djspawnbrest/ESP32AY/PCB/revD2/KiCad/3d/ZX62D-B-5P8.step

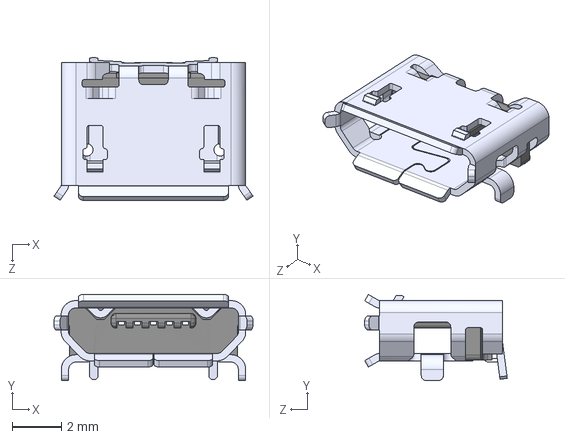
[picture p22: CAD file, 2024-06-26]
PCB/revD2/KiCad/3d/ZX62D-B-5P8.step
8.09 x 3.50 x 5.80 mm
