djspawnbrest/ESP32AY/PCB/revD2/KiCad/3d/35RAPC2BHN2.step

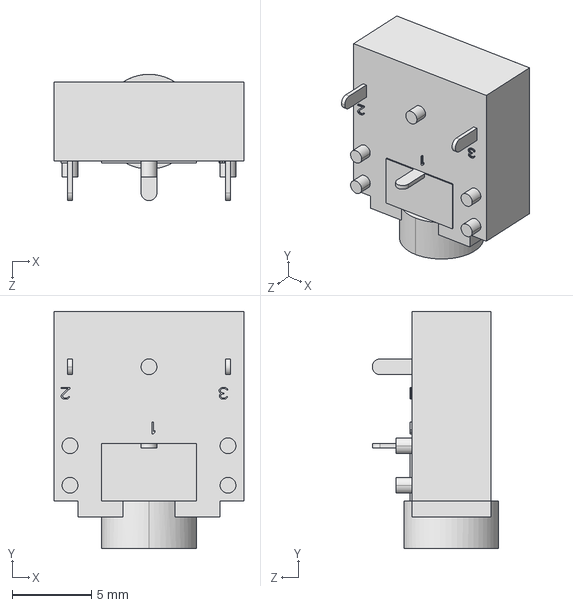
[picture p24: CAD file, 2024-06-26]
PCB/revD2/KiCad/3d/35RAPC2BHN2.step
12.0 x 15.0 x 8.00 mm
