djspawnbrest/ESP32AY/PCB/revD2/KiCad/3d/TPA6130A2RTJTG4.step

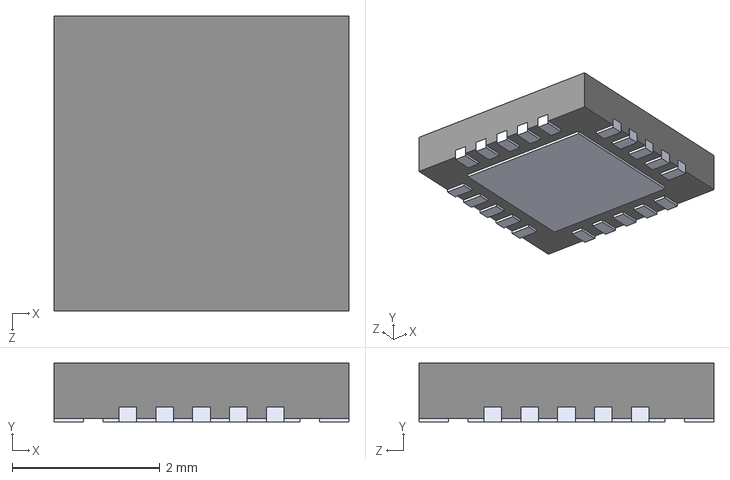
[picture p25: CAD file, 2024-06-26]
PCB/revD2/KiCad/3d/TPA6130A2RTJTG4.step
4.00 x 0.8 x 4.00 mm
