djspawnbrest/ESP32AY/PCB/revD2/KiCad/3d/FSM8J.STEP

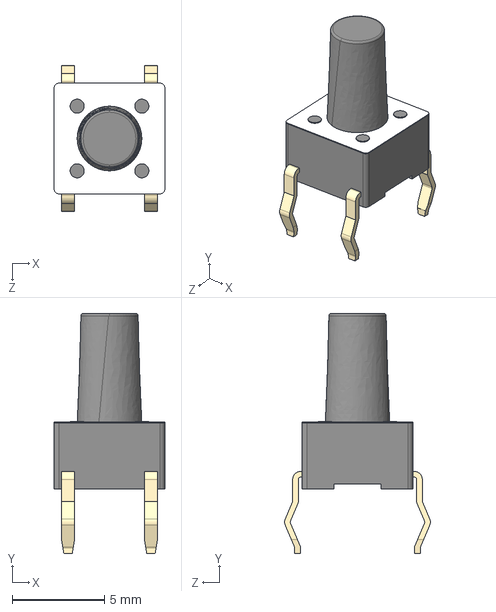
[picture p26: CAD file, 2024-06-26]
PCB/revD2/KiCad/3d/FSM8J.STEP
5.99 x 13.0 x 7.90 mm
