djspawnbrest/ESP32AY/PCB/revD2/KiCad/3d/Tactal Switch -Thru (6mmx 6mmx9.0mm).stp

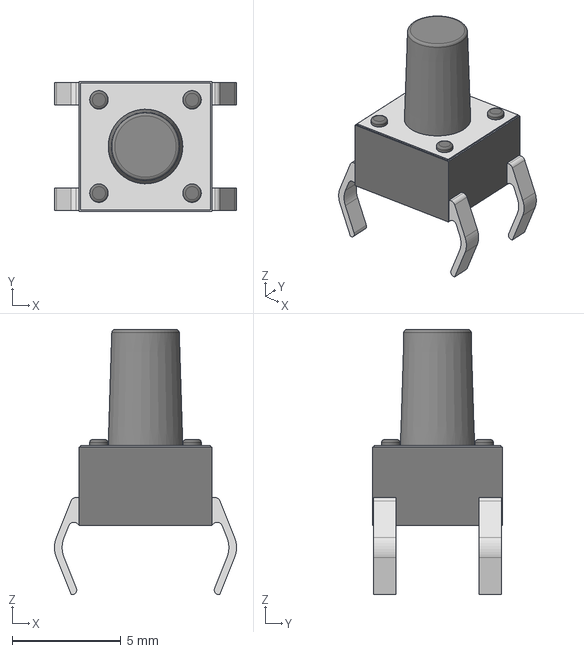
[picture p27: CAD file, 2024-06-26]
PCB/revD2/KiCad/3d/Tactal Switch -Thru (6mmx 6mmx9.0mm).stp
8.37 x 5.99 x 12.2 mm
