djspawnbrest/ESP32AY/PCB/revD2/KiCad/3d/SS14.step

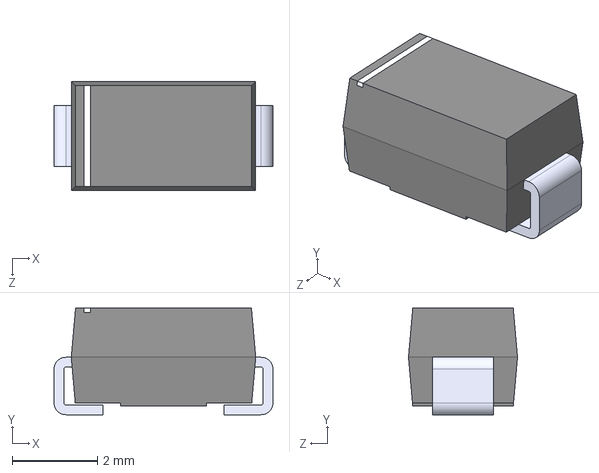
[picture p28: CAD file, 2024-06-26]
PCB/revD2/KiCad/3d/SS14.step
5.14 x 2.50 x 2.56 mm
