djspawnbrest/ESP32AY/PCB/revD2/KiCad/3d/tft1.8.step

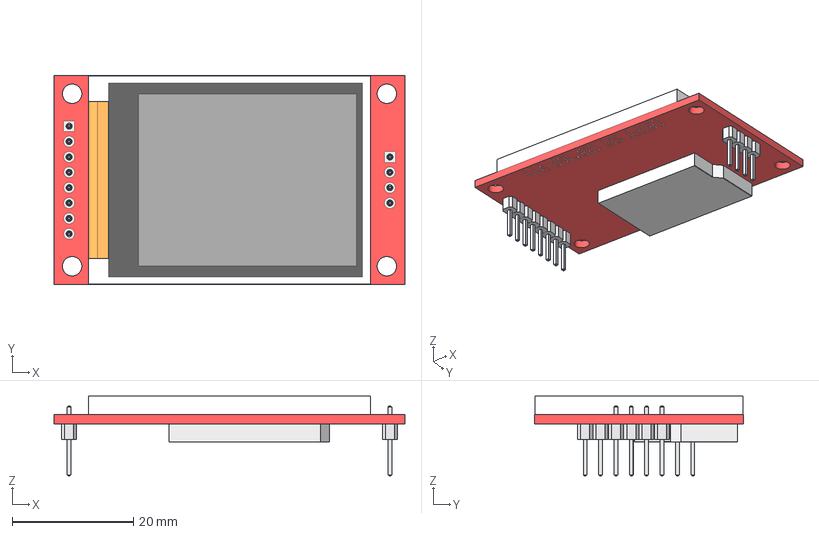
[picture p29: CAD file, 2024-06-26]
PCB/revD2/KiCad/3d/tft1.8.step
58.0 x 34.5 x 13.1 mm
1.8 TFT 128x160 SPI1_001
8pins1_001
4pins1_001
