djspawnbrest/ESP32AY/PCB/revD2/KiCad/3d/EG1213.step

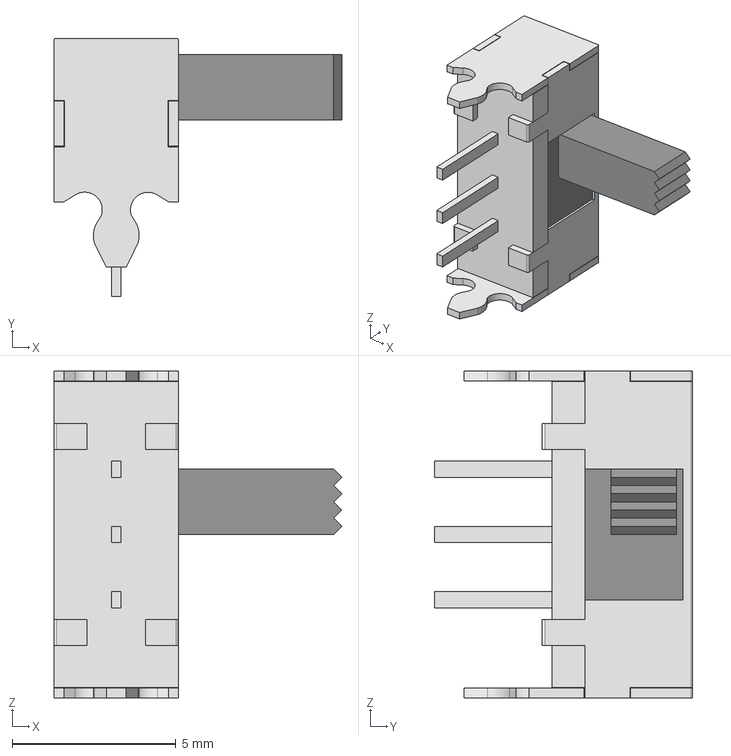
[picture p30: CAD file, 2024-06-26]
PCB/revD2/KiCad/3d/EG1213.step
8.80 x 7.90 x 10.00 mm
