djspawnbrest/ESP32AY/PCB/revD2/KiCad/3d/ME2108A33P.step

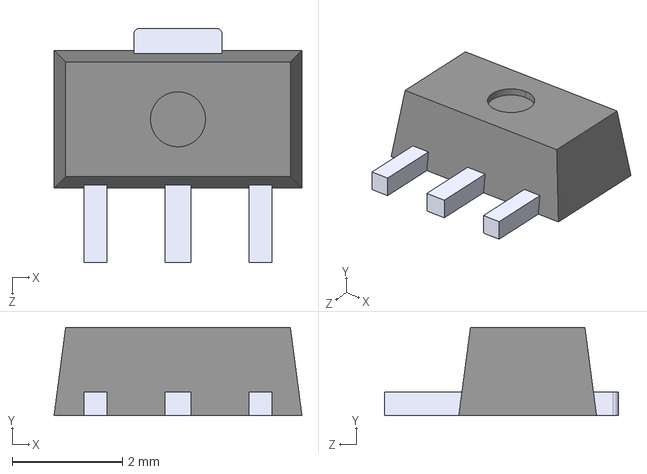
[picture p31: CAD file, 2024-06-26]
PCB/revD2/KiCad/3d/ME2108A33P.step
4.50 x 1.60 x 4.25 mm
