djspawnbrest/ESP32AY/PCB/revD2/KiCad/3d/GMT177-01.iges

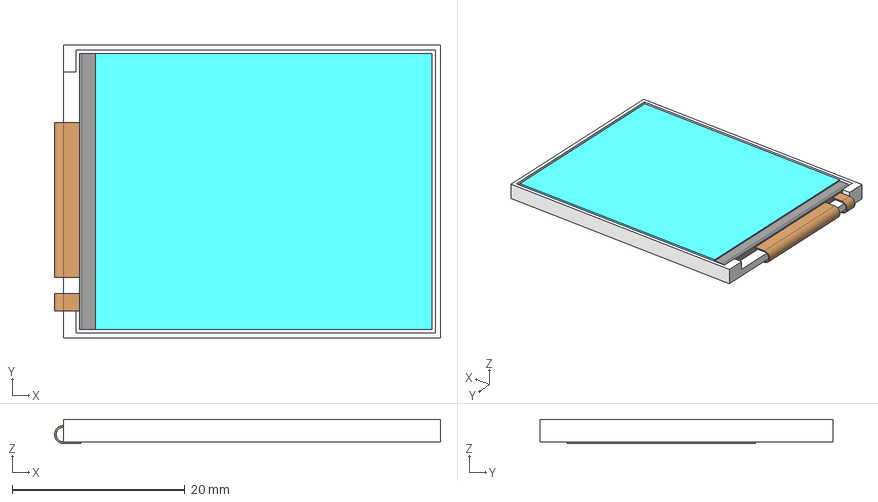
[picture p32: CAD file, 2024-06-26]
PCB/revD2/KiCad/3d/GMT177-01.iges
44.7 x 34.0 x 2.80 mm
