djspawnbrest/ESP32AY/PCB/revD2/KiCad/3d/audio_3.5mm_trrs.STEP

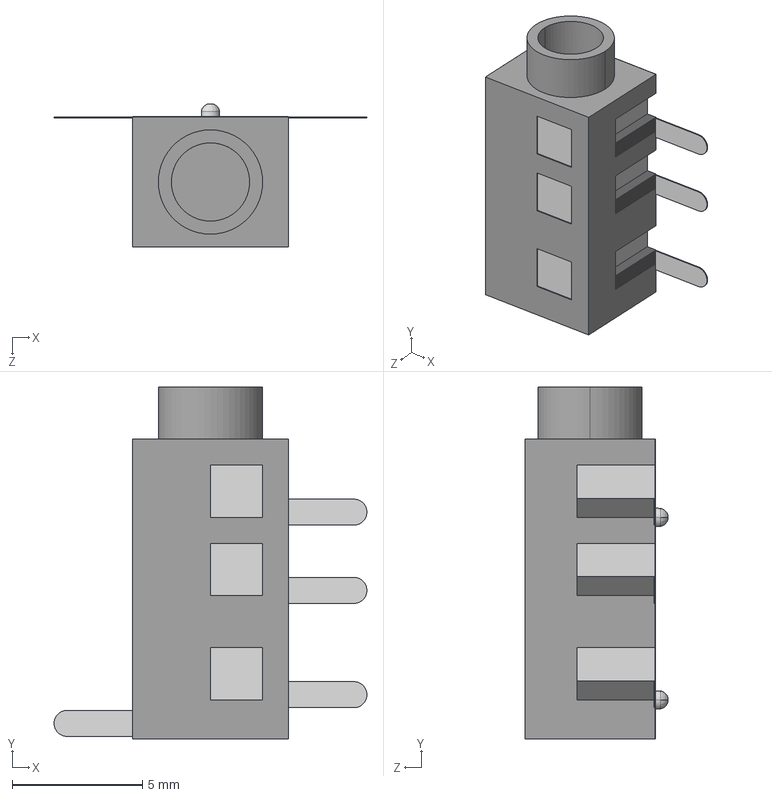
[picture p33: CAD file, 2024-06-26]
PCB/revD2/KiCad/3d/audio_3.5mm_trrs.STEP
12.0 x 13.5 x 5.50 mm
Composant1.step
audio_3.5mm_trrs.step
audio_3.5mm_trrs-0.step
audio_3.5mm_trrs-1.step
audio_3.5mm_trrs-2.step
audio_3.5mm_trrs-3.step
audio_3.5mm_trrs-4.step
audio_3.5mm_trrs-5.step
audio_3.5mm_trrs-6.step
audio_3.5mm_trrs-7.step
audio_3.5mm_trrs-8.step
audio_3.5mm_trrs-9.step
audio_3.5mm_trrs-10.step
audio_3.5mm_trrs-11.step
audio_3.5mm_trrs-12.step
audio_3.5mm_trrs-13.step
