djspawnbrest/ESP32AY/PCB/revD2/KiCad/3d/ArduinoMega_STEP_AP203.STEP

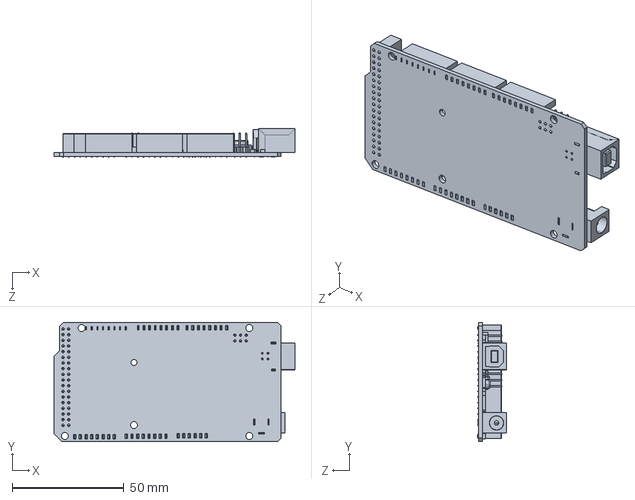
[picture p34: CAD file, 2024-06-26]
PCB/revD2/KiCad/3d/ArduinoMega_STEP_AP203.STEP
107.9 x 53.4 x 13.0 mm
