djspawnbrest/ESP32AY/PCB/revD2/KiCad/3d/EC11-THT-15_rotated.step

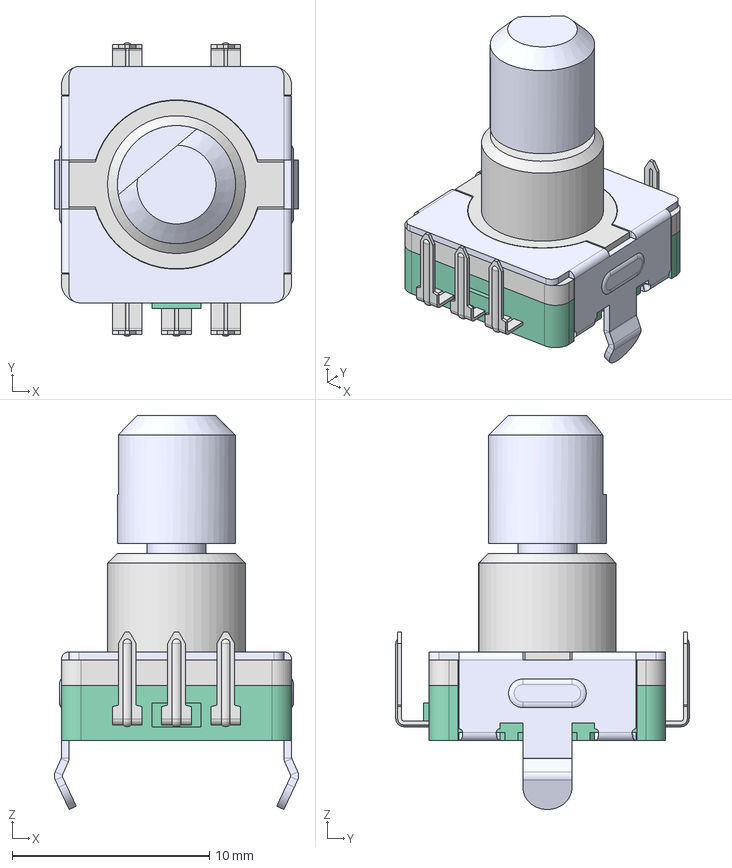
[picture p35: CAD file, 2024-06-26]
PCB/revD2/KiCad/3d/EC11-THT-15_rotated.step
12.4 x 14.9 x 20.0 mm
EC11-Base
EC11-Shaft-F
EC11-Housing-THT
