djspawnbrest/ESP32AY/PCB/revD2/KiCad/3d/TP4056.step

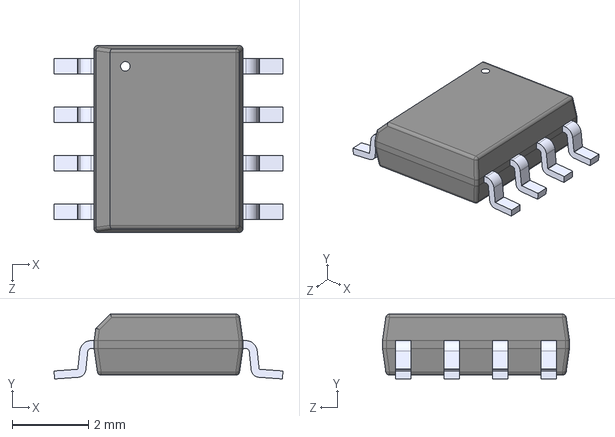
[picture p36: CAD file, 2024-06-26]
PCB/revD2/KiCad/3d/TP4056.step
6.00 x 1.70 x 4.90 mm
