djspawnbrest/ESP32AY/src/players/PT3Play.h

//Pro tracker 3.x player was written by S.V. Bulba.

//Table #0 of Pro Tracker 3.3x - 3.4r
const unsigned short PT3NoteTable_PT_33_34r[] =
{ 0x0C21, 0x0B73, 0x0ACE, 0x0A33, 0x09A0, 0x0916, 0x0893, 0x0818, 0x07A4, 0x0736, 0x06CE, 0x066D, 0x0610, 0x05B9, 0x0567, 0x0519, 0x04D0, 0x048B, 0x0449, 0x040C, 0x03D2, 0x039B, 0x0367, 0x0336, 0x0308, 0x02DC, 0x02B3, 0x028C, 0x0268, 0x0245, 0x0224, 0x0206, 0x01E9, 0x01CD, 0x01B3, 0x019B, 0x0184, 0x016E, 0x0159, 0x0146, 0x0134, 0x0122, 0x0112, 0x0103, 0x00F4, 0x00E6, 0x00D9, 0x00CD, 0x00C2, 0x00B7, 0x00AC, 0x00A3, 0x009A, 0x0091, 0x0089, 0x0081, 0x007A, 0x0073, 0x006C, 0x0066, 0x0061, 0x005B, 0x0056, 0x0051, 0x004D, 0x0048, 0x0044, 0x0040, 0x003D, 0x0039, 0x0036, 0x0033, 0x0030, 0x002D, 0x002B, 0x0028, 0x0026, 0x0024, 0x0022, 0x0020, 0x001E, 0x001C, 0x001B, 0x0019, 0x0018, 0x0016, 0x0015, 0x0014, 0x0013, 0x0012, 0x0011, 0x0010, 0x000F, 0x000E, 0x000D, 0x000C };

//{Table #0 of Pro Tracker 3.4x - 3.5x}
const unsigned short PT3NoteTable_PT_34_35[] =
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
#define PT3_SamplesPointers(x) (header->PT3_SamplesPointers0 [(x) * 2] | (header->PT3_SamplesPointers0 [(x) * 2 + 1] << 8))
#define PT3_OrnamentsPointers(x) (header->PT3_OrnamentsPointers0 [(x) * 2] | (header->PT3_OrnamentsPointers0 [(x) * 2 + 1] << 8))

struct PT3_Channel_Parameters
{
    unsigned short Address_In_Pattern, OrnamentPointer, SamplePointer, Ton;
    unsigned char Loop_Ornament_Position, Ornament_Length, Position_In_Ornament, Loop_Sample_Position, Sample_Length, Position_In_Sample, Volume, Number_Of_Notes_To_Skip, Note, Slide_To_Note, Amplitude;
    bool Envelope_Enabled, Enabled, SimpleGliss;
    short Current_Amplitude_Sliding, Current_Noise_Sliding, Current_Envelope_Sliding, Ton_Slide_Count, Current_OnOff, OnOff_Delay, OffOn_Delay, Ton_Slide_Delay, Current_Ton_Sliding, Ton_Accumulator, Ton_Slide_Step, Ton_Delta;
    signed char Note_Skip_Counter;
};

struct PT3_Parameters
{
    unsigned char Env_Base_lo;
    unsigned char Env_Base_hi;
    short Cur_Env_Slide, Env_Slide_Add;
    signed char Cur_Env_Delay, Env_Delay;
    unsigned char Noise_Base, Delay, AddToNoise, DelayCounter, CurrentPosition;
    int Version;
};

struct PT3_SongInfo
{
    PT3_Parameters PT3;
    PT3_Channel_Parameters PT3_A, PT3_B, PT3_C;
};

#define PT3_A ((PT3_SongInfo *)data)->PT3_A
#define PT3_B ((PT3_SongInfo *)data)->PT3_B
#define PT3_C ((PT3_SongInfo *)data)->PT3_C
#define PT3 ((PT3_SongInfo *)data)->PT3

#define GET_COMMON_VARS(x) \
    unsigned char *module;\
    PT3_File *header;\
    void *data;\
    if(!info.is_ts || x == 0)\
    {\
        module = info.module;\
        header = (PT3_File *)info.module;\
        data = info.data;\
    }\
    else\
    {\
        module = info.module1;\
        header = (PT3_File *)info.module1;\
        data = info.data1;\
    }

bool PT3_Detect(unsigned char *module, unsigned long length);

unsigned char *PT3_FindSig(unsigned char *buffer, long length)
{
    char sig[] =
    { 0x50, 0x72, 0x6f, 0x54, 0x72, 0x61, 0x63, 0x6b, 0x65, 0x72, 0x20, 0x33, 0x2e };
    char sig1[] =
    { 0x56, 0x6f, 0x72, 0x74, 0x65, 0x78, 0x20, 0x54, 0x72, 0x61, 0x63, 0x6b, 0x65, 0x72, 0x20, 0x49, 0x49 };
    if(length < sizeof(sig) || length < sizeof(sig1))
        return 0;
    unsigned char *ptr = buffer;
    unsigned long remaining = length - sizeof(sig);
    while(remaining > sizeof(sig))
    {
        if(!memcmp(ptr, sig, sizeof(sig)) || !memcmp(ptr, sig1, sizeof(sig1))) //found
        {
            return ptr;
        }
        ptr++;
        remaining--;
    }
    return 0;
}

void PT3_Init(AYSongInfo &info)
{
    int i;
    unsigned char b;
    unsigned char *module = info.module;
    PT3_File *header = (PT3_File *)module;
    if(info.data)
    {
        delete (PT3_SongInfo *)info.data;
        info.data = 0;
    }
    if(info.data1)
    {
        delete (PT3_SongInfo *)info.data1;
        info.data1 = 0;
    }
    info.data = (void *)new PT3_SongInfo;
    if(!info.data)
        return;
    memset(info.data, 0, sizeof(PT3_SongInfo));

    int version = 6;

    if((header->PT3_MusicName[13] >= '0') && (header->PT3_MusicName[13] <= '9'))
    {
        version = header->PT3_MusicName[13] - 0x30;
    }
    
    bool is_ts_37 = false;
    if(version >= 7)
    {
        for(int pos = 0; pos < header->PT3_NumberOfPositions && pos < 256; pos++)
        {
            int pat_idx = header->PT3_PositionList[pos] / 3;
            if(pat_idx >= 24 && pat_idx < 48)
            {
                is_ts_37 = true;
                break;
            }
        }
    }
    
    unsigned char *ptr = PT3_FindSig(module + 0x63, info.module_len - 0x63);
    if((unsigned long)ptr > 0 || is_ts_37)
    {
        info.is_ts = true;
        if(is_ts_37 && (unsigned long)ptr == 0)
        {
            info.module1 = module;
        }
        else
        {
            info.module1 = ptr;
            is_ts_37 = false;
        }
        info.data1 = (void *)new PT3_SongInfo;
        if(!info.data1)
        {
            delete (PT3_SongInfo *)info.data;
            info.data = 0;
            return;
        }
        memset(info.data1, 0, sizeof(PT3_SongInfo));
    }

    void *data = info.data;
    module = info.module;

    for(unsigned long y = 0; y < 2; y++)
    {
        PT3.CurrentPosition = 0;
        i = header->PT3_PositionList[0];
        b = header->PT3_MusicName[0x62];
        if(b != 0x20)
        {
            int max_pos = b * 3 - 3;
            i = max_pos - i;
        }
        if(is_ts_37 && y == 1)
        {
            int pat_idx = i / 3;
            pat_idx = 47 - pat_idx;
            i = pat_idx * 3;
        }
        PT3.Version = version;
        PT3.DelayCounter = 1;
        PT3.Delay = header->PT3_Delay;
        PT3_A.Address_In_Pattern = ay_sys_getword(&module[PT3_PatternsPointer + i * 2]);
        PT3_B.Address_In_Pattern = ay_sys_getword(&module[PT3_PatternsPointer + i * 2 + 2]);
        PT3_C.Address_In_Pattern = ay_sys_getword(&module[PT3_PatternsPointer + i * 2 + 4]);

        PT3_A.OrnamentPointer = PT3_OrnamentsPointers(0);
        PT3_A.Loop_Ornament_Position = module[PT3_A.OrnamentPointer];
        PT3_A.OrnamentPointer++;
        PT3_A.Ornament_Length = module[PT3_A.OrnamentPointer];
        PT3_A.OrnamentPointer++;
        PT3_A.SamplePointer = PT3_SamplesPointers(1);
        PT3_A.Loop_Sample_Position = module[PT3_A.SamplePointer];
        PT3_A.SamplePointer++;
        PT3_A.Sample_Length = module[PT3_A.SamplePointer];
        PT3_A.SamplePointer++;
        PT3_A.Volume = 15;
        PT3_A.Note_Skip_Counter = 1;

        PT3_B.OrnamentPointer = PT3_A.OrnamentPointer;
        PT3_B.Loop_Ornament_Position = PT3_A.Loop_Ornament_Position;
        PT3_B.Ornament_Length = PT3_A.Ornament_Length;
        PT3_B.SamplePointer = PT3_A.SamplePointer;
        PT3_B.Loop_Sample_Position = PT3_A.Loop_Sample_Position;
        PT3_B.Sample_Length = PT3_A.Sample_Length;
        PT3_B.Volume = 15;
        PT3_B.Note_Skip_Counter = 1;

        PT3_C.OrnamentPointer = PT3_A.OrnamentPointer;
        PT3_C.Loop_Ornament_Position = PT3_A.Loop_Ornament_Position;
        PT3_C.Ornament_Length = PT3_A.Ornament_Length;
        PT3_C.SamplePointer = PT3_A.SamplePointer;
        PT3_C.Loop_Sample_Position = PT3_A.Loop_Sample_Position;
        PT3_C.Sample_Length = PT3_A.Sample_Length;
        PT3_C.Volume = 15;
        PT3_C.Note_Skip_Counter = 1;
        if(!info.is_ts)
            break;
        data = info.data1;
        if(!is_ts_37)
        {
            module = info.module1;
            header = (PT3_File *)module;
        }
    }

    ay_resetay(&info, 0);
    ay_resetay(&info, 1);
}

int PT3_GetNoteFreq(AYSongInfo &info, unsigned char j, unsigned long chip_num)
{
    GET_COMMON_VARS(chip_num);
    switch(header->PT3_TonTableId)
    {
        case 0:
            if(PT3.Version <= 3)
                return PT3NoteTable_PT_33_34r[j];
            else
                return PT3NoteTable_PT_34_35[j];
        case 1:
            return PT3NoteTable_ST[j];
        case 2:
            if(PT3.Version <= 3)
                return PT3NoteTable_ASM_34r[j];
            else
                return PT3NoteTable_ASM_34_35[j];
        default:
            if(PT3.Version <= 3)
                return PT3NoteTable_REAL_34r[j];
            else
                return PT3NoteTable_REAL_34_35[j];
    }
}

void PT3_PatternIntterpreter(AYSongInfo &info, PT3_Channel_Parameters &chan, unsigned long chip_num)
{
    GET_COMMON_VARS(chip_num);
    bool quit;
    unsigned char flag9, flag8, flag5, flag4, flag3, flag2, flag1;
    unsigned char counter;
    int prnote, prsliding;
    prnote = chan.Note;
    prsliding = chan.Current_Ton_Sliding;
    quit = false;
    counter = 0;
    flag9 = flag8 = flag5 = flag4 = flag3 = flag2 = flag1 = 0;
    do
    {
        unsigned char val = module[chan.Address_In_Pattern];
        if(val >= 0xf0)
        {
            chan.OrnamentPointer = PT3_OrnamentsPointers((val - 0xf0));
            chan.Loop_Ornament_Position = module[chan.OrnamentPointer];
            chan.OrnamentPointer++;
            chan.Ornament_Length = module[chan.OrnamentPointer];
            chan.OrnamentPointer++;
            chan.Address_In_Pattern++;
            chan.SamplePointer = PT3_SamplesPointers((module [chan.Address_In_Pattern] / 2));
            chan.Loop_Sample_Position = module[chan.SamplePointer];
            chan.SamplePointer++;
            chan.Sample_Length = module[chan.SamplePointer];
            chan.SamplePointer++;
            chan.Envelope_Enabled = false;
            chan.Position_In_Ornament = 0;
        }
        else if(val >= 0xd1 && val <= 0xef)
        {
            chan.SamplePointer = PT3_SamplesPointers((val - 0xd0));
            chan.Loop_Sample_Position = module[chan.SamplePointer];
            chan.SamplePointer++;
            chan.Sample_Length = module[chan.SamplePointer];
            chan.SamplePointer++;
        }
        else if(val == 0xd0)
        {
            quit = true;
        }
        else if(val >= 0xc1 && val <= 0xcf)
        {
            chan.Volume = val - 0xc0;
        }
        else if(val == 0xc0)
        {
            chan.Position_In_Sample = 0;
            chan.Current_Amplitude_Sliding = 0;
            chan.Current_Noise_Sliding = 0;
            chan.Current_Envelope_Sliding = 0;
            chan.Position_In_Ornament = 0;
            chan.Ton_Slide_Count = 0;
            chan.Current_Ton_Sliding = 0;
            chan.Ton_Accumulator = 0;
            chan.Current_OnOff = 0;
            chan.Enabled = false;
            quit = true;
        }
        else if(val >= 0xb2 && val <= 0xbf)
        {
            chan.Envelope_Enabled = true;
            ay_writeay(&info, AY_ENV_SHAPE, val - 0xb1, chip_num);
            chan.Address_In_Pattern++;
            PT3.Env_Base_hi = module[chan.Address_In_Pattern];
            chan.Address_In_Pattern++;
            PT3.Env_Base_lo = module[chan.Address_In_Pattern];
            chan.Position_In_Ornament = 0;
            PT3.Cur_Env_Slide = 0;
            PT3.Cur_Env_Delay = 0;
        }
        else if(val == 0xb1)
        {
            chan.Address_In_Pattern++;
            chan.Number_Of_Notes_To_Skip = module[chan.Address_In_Pattern];
        }
        else if(val == 0xb0)
        {
            chan.Envelope_Enabled = false;
            chan.Position_In_Ornament = 0;
        }
        else if(val >= 0x50 && val <= 0xaf)
        {
            chan.Note = val - 0x50;
            chan.Position_In_Sample = 0;
            chan.Current_Amplitude_Sliding = 0;
            chan.Current_Noise_Sliding = 0;
            chan.Current_Envelope_Sliding = 0;
            chan.Position_In_Ornament = 0;
            chan.Ton_Slide_Count = 0;
            chan.Current_Ton_Sliding = 0;
            chan.Ton_Accumulator = 0;
            chan.Current_OnOff = 0;
            chan.Enabled = true;
            quit = true;
        }
        else if(val >= 0x40 && val <= 0x4f)
        {
            chan.OrnamentPointer = PT3_OrnamentsPointers((val - 0x40));
            chan.Loop_Ornament_Position = module[chan.OrnamentPointer];
            chan.OrnamentPointer++;
            chan.Ornament_Length = module[chan.OrnamentPointer];
            chan.OrnamentPointer++;
            chan.Position_In_Ornament = 0;
        }
        else if(val >= 0x20 && val <= 0x3f)
        {
            PT3.Noise_Base = val - 0x20;
        }
        else if(val >= 0x10 && val <= 0x1f)
        {
            if(val == 0x10)
                chan.Envelope_Enabled = false;
            else
            {
                ay_writeay(&info, AY_ENV_SHAPE, val - 0x10, chip_num);
                chan.Address_In_Pattern++;
                PT3.Env_Base_hi = module[chan.Address_In_Pattern];
                chan.Address_In_Pattern++;
                PT3.Env_Base_lo = module[chan.Address_In_Pattern];
                chan.Envelope_Enabled = true;
                PT3.Cur_Env_Slide = 0;
                PT3.Cur_Env_Delay = 0;
            }
            chan.Address_In_Pattern++;
            chan.SamplePointer = PT3_SamplesPointers((module [chan.Address_In_Pattern] / 2));
            chan.Loop_Sample_Position = module[chan.SamplePointer];
            chan.SamplePointer++;
            chan.Sample_Length = module[chan.SamplePointer];
            chan.SamplePointer++;
            chan.Position_In_Ornament = 0;
        }
        else if(val == 0x9)
        {
            counter++;
            flag9 = counter;
        }
        else if(val == 0x8)
        {
            counter++;
            flag8 = counter;
        }
        else if(val == 0x5)
        {
            counter++;
            flag5 = counter;
        }
        else if(val == 0x4)
        {
            counter++;
            flag4 = counter;
        }
        else if(val == 0x3)
        {
            counter++;
            flag3 = counter;
        }
        else if(val == 0x2)
        {
            counter++;
            flag2 = counter;
        }
        else if(val == 0x1)
        {
            counter++;
            flag1 = counter;
        }
        chan.Address_In_Pattern++;
    }
    while(!quit);

    while(counter > 0)
    {
        if(counter == flag1)
        {
            chan.Ton_Slide_Delay = module[chan.Address_In_Pattern];
            chan.Ton_Slide_Count = chan.Ton_Slide_Delay;
            chan.Address_In_Pattern++;
            chan.Ton_Slide_Step = ay_sys_getword(&module[chan.Address_In_Pattern]);
            chan.Address_In_Pattern += 2;
            chan.SimpleGliss = true;
            chan.Current_OnOff = 0;
            if((chan.Ton_Slide_Count == 0) && (PT3.Version >= 7))
                chan.Ton_Slide_Count++;
        }
        else if(counter == flag2)
        {
            chan.SimpleGliss = false;
            chan.Current_OnOff = 0;
            chan.Ton_Slide_Delay = module[chan.Address_In_Pattern];
            chan.Ton_Slide_Count = chan.Ton_Slide_Delay;
            chan.Address_In_Pattern += 3;
            chan.Ton_Slide_Step = abs(short(ay_sys_getword(&module[chan.Address_In_Pattern])));
            chan.Address_In_Pattern += 2;
            chan.Ton_Delta = PT3_GetNoteFreq(info, chan.Note, chip_num) - PT3_GetNoteFreq(info, prnote, chip_num);
            chan.Slide_To_Note = chan.Note;
            chan.Note = prnote;
            if(PT3.Version >= 6)
                chan.Current_Ton_Sliding = prsliding;
            if((chan.Ton_Delta - chan.Current_Ton_Sliding) < 0)
                chan.Ton_Slide_Step = -chan.Ton_Slide_Step;
        }
        else if(counter == flag3)
        {
            chan.Position_In_Sample = module[chan.Address_In_Pattern];
            chan.Address_In_Pattern++;
        }
        else if(counter == flag4)
        {
            chan.Position_In_Ornament = module[chan.Address_In_Pattern];
            chan.Address_In_Pattern++;
        }
        else if(counter == flag5)
        {
            chan.OnOff_Delay = module[chan.Address_In_Pattern];
            chan.Address_In_Pattern++;
            chan.OffOn_Delay = module[chan.Address_In_Pattern];
            chan.Current_OnOff = chan.OnOff_Delay;
            chan.Address_In_Pattern++;
            chan.Ton_Slide_Count = 0;
            chan.Current_Ton_Sliding = 0;
        }
        else if(counter == flag8)
        {
            PT3.Env_Delay = module[chan.Address_In_Pattern];
            PT3.Cur_Env_Delay = PT3.Env_Delay;
            chan.Address_In_Pattern++;
            PT3.Env_Slide_Add = ay_sys_getword(&module[chan.Address_In_Pattern]);
            chan.Address_In_Pattern += 2;
        }
        else if(counter == flag9)
        {
            PT3.Delay = module[chan.Address_In_Pattern];
            chan.Address_In_Pattern++;
        }
        counter--;
    }
    chan.Note_Skip_Counter = chan.Number_Of_Notes_To_Skip;
}

void PT3_ChangeRegisters(AYSongInfo &info, PT3_Channel_Parameters &chan, char &AddToEnv, unsigned char &TempMixer, unsigned long chip_num)
{
    GET_COMMON_VARS(chip_num);
    unsigned char j, b1, b0;
    unsigned short w;
    if(chan.Enabled)
    {
        chan.Ton = ay_sys_getword(&module[chan.SamplePointer + chan.Position_In_Sample * 4 + 2]);
        chan.Ton += chan.Ton_Accumulator;
        b0 = module[chan.SamplePointer + chan.Position_In_Sample * 4];
        b1 = module[chan.SamplePointer + chan.Position_In_Sample * 4 + 1];
        if((b1 & 0x40) != 0)
        {
            chan.Ton_Accumulator = chan.Ton;
        }
        j = chan.Note + module[chan.OrnamentPointer + chan.Position_In_Ornament];
        if((signed char)(j) < 0)
            j = 0;
        else if(j > 95)
            j = 95;
        w = PT3_GetNoteFreq(info, j, chip_num);
        chan.Ton = (chan.Ton + chan.Current_Ton_Sliding + w) & 0xfff;
        if(chan.Ton_Slide_Count > 0)
        {
            chan.Ton_Slide_Count--;
            if(chan.Ton_Slide_Count == 0)
            {
                chan.Current_Ton_Sliding += chan.Ton_Slide_Step;
                chan.Ton_Slide_Count = chan.Ton_Slide_Delay;
                if(!chan.SimpleGliss)
                {
                    if(((chan.Ton_Slide_Step < 0) && (chan.Current_Ton_Sliding <= chan.Ton_Delta)) || ((chan.Ton_Slide_Step >= 0) && (chan.Current_Ton_Sliding >= chan.Ton_Delta)))
                    {
                        chan.Note = chan.Slide_To_Note;
                        chan.Ton_Slide_Count = 0;
                        chan.Current_Ton_Sliding = 0;
                    }
                }
            }
        }
        chan.Amplitude = b1 & 0xf;
        if((b0 & 0x80) != 0)
        {
            if((b0 & 0x40) != 0)
            {
                if(chan.Current_Amplitude_Sliding < 15)
                    chan.Current_Amplitude_Sliding++;
            }
            else if(chan.Current_Amplitude_Sliding > -15)
            {
                chan.Current_Amplitude_Sliding--;
            }
        }
        chan.Amplitude += chan.Current_Amplitude_Sliding;
        if((signed char)(chan.Amplitude) < 0)
            chan.Amplitude = 0;
        else if(chan.Amplitude > 15)
            chan.Amplitude = 15;
        if(PT3.Version <= 4)
            chan.Amplitude = PT3VolumeTable_33_34[chan.Volume][chan.Amplitude];
        else
            chan.Amplitude = PT3VolumeTable_35[chan.Volume][chan.Amplitude];
        if(((b0 & 1) == 0) && chan.Envelope_Enabled)
            chan.Amplitude = chan.Amplitude | 16;
        if((b1 & 0x80) != 0)
        {
            if((b0 & 0x20) != 0)
                j = ((b0 >> 1) | 0xf0) + chan.Current_Envelope_Sliding;
            else
                j = ((b0 >> 1) & 0xf) + chan.Current_Envelope_Sliding;
            if((b1 & 0x20) != 0)
                chan.Current_Envelope_Sliding = j;
            AddToEnv += j;
        }
        else
        {
            PT3.AddToNoise = (b0 >> 1) + chan.Current_Noise_Sliding;
            if((b1 & 0x20) != 0)
                chan.Current_Noise_Sliding = PT3.AddToNoise;
        }
        TempMixer = ((b1 >> 1) & 0x48) | TempMixer;
        chan.Position_In_Sample++;
        if(chan.Position_In_Sample >= chan.Sample_Length)
            chan.Position_In_Sample = chan.Loop_Sample_Position;
        chan.Position_In_Ornament++;
        if(chan.Position_In_Ornament >= chan.Ornament_Length)
            chan.Position_In_Ornament = chan.Loop_Ornament_Position;
    }
    else
        chan.Amplitude = 0;
    TempMixer = TempMixer >> 1;
    if(chan.Current_OnOff > 0)
    {
        chan.Current_OnOff--;
        if(chan.Current_OnOff == 0)
        {
            chan.Enabled = !chan.Enabled;
            if(chan.Enabled)
                chan.Current_OnOff = chan.OnOff_Delay;
            else
                chan.Current_OnOff = chan.OffOn_Delay;
        }
    }
}

void PT3_Play_Chip(AYSongInfo &info, unsigned long chip_num)
{
    GET_COMMON_VARS(chip_num);
    unsigned char TempMixer;
    char AddToEnv;

    PT3.DelayCounter--;
    if(PT3.DelayCounter == 0)
    {
        PT3_A.Note_Skip_Counter--;
        if(PT3_A.Note_Skip_Counter == 0)
        {
            if(module[PT3_A.Address_In_Pattern] == 0)
            {
                PT3.CurrentPosition++;
                if(PT3.CurrentPosition == header->PT3_NumberOfPositions)
                    PT3.CurrentPosition = header->PT3_LoopPosition;
                int pos_val = header->PT3_PositionList[PT3.CurrentPosition];
                if(PT3.Version >= 7 && info.module1 == info.module)
                {
                    unsigned char b = header->PT3_MusicName[0x62];
                    if(b != 0x20)
                    {
                        int max_pos = b * 3 - 3;
                        pos_val = max_pos - pos_val;
                    }
                    int pat_idx = pos_val / 3;
                    if(chip_num == 1)
                    {
                        pat_idx = 47 - pat_idx;
                        pos_val = pat_idx * 3;
                    }
                }
                PT3_A.Address_In_Pattern = ay_sys_getword(&module[PT3_PatternsPointer + pos_val * 2]);
                PT3_B.Address_In_Pattern = ay_sys_getword(&module[PT3_PatternsPointer + pos_val * 2 + 2]);
                PT3_C.Address_In_Pattern = ay_sys_getword(&module[PT3_PatternsPointer + pos_val * 2 + 4]);
                PT3.Noise_Base = 0;
            }
            PT3_PatternIntterpreter(info, PT3_A, chip_num);
        }
        PT3_B.Note_Skip_Counter--;
        if(PT3_B.Note_Skip_Counter == 0)
            PT3_PatternIntterpreter(info, PT3_B, chip_num);
        PT3_C.Note_Skip_Counter--;
        if(PT3_C.Note_Skip_Counter == 0)
            PT3_PatternIntterpreter(info, PT3_C, chip_num);
        PT3.DelayCounter = PT3.Delay;
    }

    AddToEnv = 0;
    TempMixer = 0;
    PT3_ChangeRegisters(info, PT3_A, AddToEnv, TempMixer, chip_num);
    PT3_ChangeRegisters(info, PT3_B, AddToEnv, TempMixer, chip_num);
    PT3_ChangeRegisters(info, PT3_C, AddToEnv, TempMixer, chip_num);

    ay_writeay(&info, AY_MIXER, TempMixer, chip_num);

    ay_writeay(&info, AY_CHNL_A_FINE, PT3_A.Ton & 0xff, chip_num);
    ay_writeay(&info, AY_CHNL_A_COARSE, (PT3_A.Ton >> 8) & 0xf, chip_num);
    ay_writeay(&info, AY_CHNL_B_FINE, PT3_B.Ton & 0xff, chip_num);
    ay_writeay(&info, AY_CHNL_B_COARSE, (PT3_B.Ton >> 8) & 0xf, chip_num);
    ay_writeay(&info, AY_CHNL_C_FINE, PT3_C.Ton & 0xff, chip_num);
    ay_writeay(&info, AY_CHNL_C_COARSE, (PT3_C.Ton >> 8) & 0xf, chip_num);
    ay_writeay(&info, AY_CHNL_A_VOL, PT3_A.Amplitude, chip_num);
    ay_writeay(&info, AY_CHNL_B_VOL, PT3_B.Amplitude, chip_num);
    ay_writeay(&info, AY_CHNL_C_VOL, PT3_C.Amplitude, chip_num);

    ay_writeay(&info, AY_NOISE_PERIOD, (PT3.Noise_Base + PT3.AddToNoise) & 31, chip_num);
    unsigned short cur_env = ay_sys_getword(&PT3.Env_Base_lo) + AddToEnv + PT3.Cur_Env_Slide;
    ay_writeay(&info, AY_ENV_FINE, cur_env & 0xff, chip_num);
    ay_writeay(&info, AY_ENV_COARSE, (cur_env >> 8) & 0xff, chip_num);

    if(PT3.Cur_Env_Delay > 0)
    {
        PT3.Cur_Env_Delay--;
        if(PT3.Cur_Env_Delay == 0)
        {
            PT3.Cur_Env_Delay = PT3.Env_Delay;
            PT3.Cur_Env_Slide += PT3.Env_Slide_Add;
        }
    }
}

void PT3_Play(AYSongInfo &info)
{
    PT3_Play_Chip(info, 0);
    if(info.is_ts)
        PT3_Play_Chip(info, 1);
}

unsigned long PT3_GetTime(unsigned char *module, unsigned long &Loop)
{
    char a1, a2, a3, a11, a22, a33;
    unsigned long j1, j2, j3;
    int c1, c2, c3, c4, c5, c8;
    long i, j, tm = 0;
    unsigned char b;
    PT3_File *header = (PT3_File *)module;
    unsigned char ptDelay = header->PT3_Delay;
    unsigned char ptNumPos = header->PT3_NumberOfPositions;
    unsigned short ptLoopPos = header->PT3_LoopPosition;
    unsigned short ptPatPt = PT3_PatternsPointer;
    const unsigned char *ptPosList = (unsigned char *)&header->PT3_PositionList[0];

    b = ptDelay;
    a11 = a22 = a33 = 1;
    for(i = 0; i < ptNumPos; i++)
    {
        if(i == ptLoopPos)
        {
            Loop = tm;
        }
        j1 = ay_sys_getword(&module[ptPatPt + ptPosList[i] * 2]);
        j2 = ay_sys_getword(&module[ptPatPt + ptPosList[i] * 2 + 2]);
        j3 = ay_sys_getword(&module[ptPatPt + ptPosList[i] * 2 + 4]);
        a1 = a2 = a3 = 1;
        do
        {
            a1--;
            if(a1 == 0)
            {
                if(module[j1] == 0)
                    break;
                j = c1 = c2 = c3 = c4 = c5 = c8 = 0;
                do
                {
                    unsigned char val = module[j1];
                    if(val == 0xd0 || val == 0xc0 || (val >= 0x50 && val <= 0xaf))
                    {
                        a1 = a11;
                        j1++;
                        break;
                    }
                    else if(val == 0x10 || val >= 0xf0)
                    {
                        j1++;
                    }
                    else if(val >= 0xb2 && val <= 0xbf)
                    {
                        j1 += 2;
                    }
                    else if(val == 0xb1)
                    {
                        j1++;
                        a11 = module[j1];
                    }
                    else if(val >= 0x11 && val <= 0x1f)
                    {
                        j1 += 3;
                    }
                    else
                    {
                        switch(val)
                        {
                            case 1:
                                j++;
                                c1 = j;
                                break;
                            case 2:
                                j++;
                                c2 = j;
                                break;
                            case 3:
                                j++;
                                c3 = j;
                                break;
                            case 4:
                                j++;
                                c4 = j;
                                break;
                            case 5:
                                j++;
                                c5 = j;
                                break;
                            case 8:
                                j++;
                                c8 = j;
                                break;
                            case 9:
                                j++;
                                break;
                            default:
                                break;
                        }
                    }
                    j1++;
                }
                while(true);

                while(j > 0)
                {
                    if(j == c1 || j == c8)
                    {
                        j1 += 3;
                    }
                    else if(j == c2)
                    {
                        j1 += 5;
                    }
                    else if(j == c3 || j == c4)
                    {
                        j1++;
                    }
                    else if(j == c5)
                    {
                        j1 += 2;
                    }
                    else
                    {
                        b = module[j1];
                        j1++;
                    }
                    j--;
                }
            }
            a2--;
            if(a2 == 0)
            {
                j = c1 = c2 = c3 = c4 = c5 = c8 = 0;
                do
                {
                    unsigned char val = module[j2];
                    if(val == 0xd0 || val == 0xc0 || (val >= 0x50 && val <= 0xaf))
                    {
                        a2 = a22;
                        j2++;
                        break;
                    }
                    else if(val == 0x10 || val >= 0xf0)
                    {
                        j2++;
                    }
                    else if(val >= 0xb2 && val <= 0xbf)
                    {
                        j2 += 2;
                    }
                    else if(val == 0xb1)
                    {
                        j2++;
                        a22 = module[j2];
                    }
                    else if(val >= 0x11 && val <= 0x1f)
                    {
                        j2 += 3;
                    }
                    else
                    {
                        switch(val)
                        {
                            case 1:
                                j++;
                                c1 = j;
                                break;
                            case 2:
                                j++;
                                c2 = j;
                                break;
                            case 3:
                                j++;
                                c3 = j;
                                break;
                            case 4:
                                j++;
                                c4 = j;
                                break;
                            case 5:
                                j++;
                                c5 = j;
                                break;
                            case 8:
                                j++;
                                c8 = j;
                                break;
                            case 9:
                                j++;
                                break;
                            default:
                                break;
                        }
                    }
                    j2++;
                }
                while(true);
                while(j > 0)
                {
                    if(j == c1 || j == c8)
                    {
                        j2 += 3;
                    }
                    else if(j == c2)
                    {
                        j2 += 5;
                    }
                    else if(j == c3 || j == c4)
                    {
                        j2++;
                    }
                    else if(j == c5)
                    {
                        j2 += 2;
                    }
                    else
                    {
                        b = module[j2];
                        j2++;
                    }
                    j--;
                }
            }
            a3--;
            if(a3 == 0)
            {
                j = c1 = c2 = c3 = c4 = c5 = c8 = 0;
                do
                {
                    unsigned char val = module[j3];
                    if(val == 0xd0 || val == 0xc0 || (val >= 0x50 && val <= 0xaf))
                    {
                        a3 = a33;
                        j3++;
                        break;
                    }
                    else if(val == 0x10 || val >= 0xf0)
                    {
                        j3++;
                    }
                    else if(val >= 0xb2 && val <= 0xbf)
                    {
                        j3 += 2;
                    }
                    else if(val == 0xb1)
                    {
                        j3++;
                        a33 = module[j3];
                    }
                    else if(val >= 0x11 && val <= 0x1f)
                    {
                        j3 += 3;
                    }
                    else
                    {
                        switch(val)
                        {
                            case 1:
                                j++;
                                c1 = j;
                                break;
                            case 2:
                                j++;
                                c2 = j;
                                break;
                            case 3:
                                j++;
                                c3 = j;
                                break;
                            case 4:
                                j++;
                                c4 = j;
                                break;
                            case 5:
                                j++;
                                c5 = j;
                                break;
                            case 8:
                                j++;
                                c8 = j;
                                break;
                            case 9:
                                j++;
                                break;
                            default:
                                break;
                        }
                    }
                    j3++;
                }
                while(true);
                while(j > 0)
                {
                    if(j == c1 || j == c8)
                    {
                        j3 += 3;
                    }
                    else if(j == c2)
                    {
                        j3 += 5;
                    }
                    else if(j == c3 || j == c4)
                    {
                        j3++;
                    }
                    else if(j == c5)
                    {
                        j3 += 2;
                    }
                    else
                    {
                        b = module[j3];
                        j3++;
                    }
                    j--;
                }
            }
            tm += b;
        }
        while(true);

    }
    return tm;
}

void PT3_GetInfo(AYSongInfo &info)
{
    unsigned char *module = info.file_data;
    unsigned long loop = 0;
    unsigned long length = PT3_GetTime(module, loop);
    info.Length = length;
    info.Loop = loop;
    unsigned char *ptr = PT3_FindSig(module + 0x63, info.module_len - 0x63);
    if((unsigned long)ptr > 0)
    {
        length = PT3_GetTime(ptr, loop);
        if(length > info.Length)
            info.Length = length;
        if(loop < info.Loop)
            info.Loop = loop;
    }
    ptr = module + 0x1e;
    ay_sys_getstr(info.Name, sizeof(info.Name), ptr, 32);
    ptr = module + 0x42;
    ay_sys_getstr(info.Author, sizeof(info.Author), ptr, 32);
}

void PT3_Cleanup(AYSongInfo &info)
{
    if(info.data)
    {
        delete (PT3_SongInfo *)info.data;
        info.data = 0;
    }
    if(info.data1)
    {
        delete (PT3_SongInfo *)info.data1;
        info.data1 = 0;
    }
}

bool PT3_Detect(unsigned char *module, unsigned long length)
{
    int j, j1, j2;
    PT3_File *header = (PT3_File *)module;
    if(length < 202)
        return false;
    if(PT3_PatternsPointer> length)
        return false;
    if(module[PT3_PatternsPointer - 1] != 255)
        return false;
    if(PT3_OrnamentsPointers(0) + 2 > length)
        return false;

    j = 0;
    memcpy(&j, &module[PT3_OrnamentsPointers(0)], 3);
    if(j != 256)
        return false;

    j = ay_sys_getword(&module[PT3_PatternsPointer]);
    if(j > length)
        return false;
    if(j - (int)(PT3_PatternsPointer) <= 0)
        return false;
    /*if(((j - (int)(PT3_PatternsPointer)) % 6) != 0)
     return false;*/

    j1 = 0;
    j2 = 0;
    while((j2 < 256) && (j2 <= length - 201) && (header->PT3_PositionList[j2] != 255))
    {
        if((unsigned long)(j1) < header->PT3_PositionList[j2])
            j1 = header->PT3_PositionList[j2];
        if((j1 % 3) != 0)
            return false;
        j2++;
    }
    if(((j - (int)(PT3_PatternsPointer)) / 6) != ((j1 / 3) + 1))
        return false;

    j = 15;
    while((j > 0) && (PT3_OrnamentsPointers(j) == 0))
        j--;

    int F_Length = PT3_OrnamentsPointers(j) + module[PT3_OrnamentsPointers(j) + 1] + 2;
    if(F_Length > length + 1)
        return false;

    //header->PT3_NumberOfPositions = j2;
    return true;
}
