djspawnbrest/ESP32AY/src/browser.h

// browser colors
#define BRWSR_HEADER_BG TFT_BLUE      // browser header background color
#define BRWSR_HEADER_TX TFT_WHITE     // browser header text color
#define BRWSR_SORT      TFT_RED       // browser sorting label
#define BRWSR_CURSOR    TFT_RED       // browser cursor color
#define BRWSR_DIR       TFT_YELLOW    // browser dir color
#define BRWSR_PLST      ZX_WHITE_N    // browser playlists color
#define BRWSR_PLAY_DIR  TFT_BLUE      // browser playing dir color
#define BRWSR_PLAY_FILE TFT_BLUE      // browser playing file color
#define BRWSR_PLAY_PLST TFT_BLUE      // browser playing playlist color
#define BRWSR_PSG_FILE  WILD_CYAN_D2  // browser AY/YM formats color
#define BRWSR_TAP_FILE  WILD_CYAN     // browser TAP/TZX formats color
#define BRWSR_TRK_FILE  WILD_GREEN    // browser tracker music formats color
#define BRWSR_PCM_FILE  TFT_VIOLET    // browser PCM (MP3/WAV) formats color

enum{
  FILE_ERR_NONE=0,
  FILE_ERR_NO_CARD=-1,
  FILE_ERR_TOO_LARGE=-2,
  FILE_ERR_NOT_ENOUGH_MEMORY=-3,
  FILE_ERR_UNK_FORMAT=-4,
  FILE_ERR_OTHER=-5,
  FILE_ERR_NO_FILE=-6
};

#define BROWSER_LINES       18
// #define BROWSER_WAIT_SHOW   1000/10 //delay before showing wait screen

enum{
  BROWSE_DIR=0,
  BROWSE_AYL
};

enum{
  MUS=0,
  DIR,
  AYL
};

#define SORT_HASH_LEN       4
#define SORT_FILES_MAX      1280 //there are 1070 entries in the Tr_Songs/Authors currently

#define SCROLLBAR_X         232
#define SCROLLBAR_Y         24
#define SCROLLBAR_WIDTH     4
#define SCROLLBAR_HEIGHT    288

struct sortStruct{
  char hash[SORT_HASH_LEN];
  uint16_t file_id;
  uint32_t file_size;
  uint16_t mod_date;
  uint16_t mod_time;
};

sortStruct sort_list[SORT_FILES_MAX];
sortStruct sort_list_play[SORT_FILES_MAX];
int16_t sort_list_len,sort_list_play_len;
int16_t cursor_offset;
uint8_t browser_rebuild=1;

//not need semaphore
void clear_scrollbar(){
  // Очищаем область скроллбара (закрашиваем фоном)
  tft.fillRect(SCROLLBAR_X,SCROLLBAR_Y,SCROLLBAR_WIDTH,SCROLLBAR_HEIGHT,TFT_BLACK);
}

//not need semaphore
void draw_scrollbar(int current_pos,int total_items){
  if(total_items<=BROWSER_LINES) return;
  // Фон полосы прокрутки (трек)
  tft.fillRect(SCROLLBAR_X,SCROLLBAR_Y,SCROLLBAR_WIDTH,SCROLLBAR_HEIGHT,TFT_DARKGREY);
  // Расчет размера ползунка (пропорционально видимой части)
  int thumb_height=(BROWSER_LINES*SCROLLBAR_HEIGHT)/total_items;
  if(thumb_height<8) thumb_height=8;  // минимальная высота для видимости
  // Расчет позиции начала отображения (как в browser_screen)
  int id=current_pos-BROWSER_LINES/2;
  if(id>=total_items-BROWSER_LINES) id=total_items-BROWSER_LINES;
  if(id<0) id=0;
  // Позиция ползунка
  int thumb_pos=0;
  if(total_items>BROWSER_LINES){
    thumb_pos=(id*(SCROLLBAR_HEIGHT-thumb_height))/(total_items-BROWSER_LINES);
  }
  // Ползунок
  tft.fillRect(SCROLLBAR_X,SCROLLBAR_Y+thumb_pos,SCROLLBAR_WIDTH,thumb_height,TFT_WHITE);
}

//not need semaphore
void scrollString(char *txt,uint8_t textSize,uint16_t textColor,int width,int height,int xPos,int yPos,uint8_t scrollNumber=0,uint16_t bgColor=BRWSR_CURSOR,bool rounded=true){
  uint16_t strSize=tft_strlen(txt,textSize);
  if(millis()-mlsS[scrollNumber]>sUp[scrollNumber]){
    img.setColorDepth(8);
    img.createSprite(width,height);
    img.fillScreen(0);
    if(rounded){
      img.fillRoundRect(0,0,width,height,3,bgColor);
    }else{
      img.fillRect(0,0,width,height,bgColor);
    }
    img.setFreeFont(&WildFont);
    img.setTextSize(textSize);
    img.setTextWrap(false);
    img.setTextColor(textColor);
    img.setCursor((sPos[scrollNumber]-(sPos[scrollNumber]*2)),16);
    img.print(utf8rus(txt));
    sUp[scrollNumber]=sUpC[scrollNumber];
    if(strSize-sPos[scrollNumber]>=width&&scrollDir[scrollNumber]){
      sPos[scrollNumber]++;
      if(strSize-sPos[scrollNumber]<width){scrollDir[scrollNumber]=false;sUp[scrollNumber]=S_UPD_DIR;}
    }
    if(!scrollDir[scrollNumber]){
      sPos[scrollNumber]--;
      if(sPos[scrollNumber]<0){scrollDir[scrollNumber]=true;sUp[scrollNumber]=S_UPD_DIR;}
    }
    mlsS[scrollNumber]=millis();
    img.pushSprite(xPos,yPos);
    img.deleteSprite();
  }
}

//not need semaphore
int browser_check_ext(const char* name){
  for(int i=strlen(name)-1;i>=0;i--){
    if(name[i]=='.'){
      for(int j=1;j<TYPES_ALL;j++){
        if(strcasecmp(&name[i+1],file_ext_list[j])==0) return j;
      }
      break;
    }
  }
  return TYPE_UNK;
}

//not need semaphore
uint16_t get_file_type_color(const char* name){
  // mus files types
  uint16_t color;
  uint8_t mus_type=browser_check_ext(name);
  switch(mus_type){
    case TYPE_PT1:
    case TYPE_PT2:
    case TYPE_PT3:
    case TYPE_STC:
    case TYPE_STP:
    case TYPE_ASC:
    case TYPE_PSC:
    case TYPE_SQT:
    case TYPE_AY:
    case TYPE_PSG:
    case TYPE_RSF:
    case TYPE_YRG:
      color=BRWSR_PSG_FILE;
      break;
    case TYPE_MOD:
    case TYPE_S3M:
  #if defined(CONFIG_IDF_TARGET_ESP32S3)
    case TYPE_XM:
  #endif
      color=BRWSR_TRK_FILE;
      break;
    case TYPE_TAP:
    case TYPE_TZX:
      color=BRWSR_TAP_FILE;
      break;
    case TYPE_MP3:
    case TYPE_WAV:
      color=BRWSR_PCM_FILE;
      break;
    default:
      color=BRWSR_PSG_FILE;
      break;
  }
  return color;
}

//not need semaphore
void browser_reset_directory(){
  strncpy(sdConfig.active_dir,"/",sizeof(sdConfig.active_dir)-1);
  strncpy(sdConfig.prev_dir,"/",sizeof(sdConfig.prev_dir)-1);
  strncpy(sdConfig.ayl_file,"",sizeof(sdConfig.ayl_file)-1);
}

//semaphored
void browser_enter_directory(){
  if(xSemaphoreTake(sdCardSemaphore,portMAX_DELAY)==pdTRUE){
    sd_dir.open(sdConfig.active_dir,O_RDONLY);
    sd_file.open(&sd_dir,sort_list[sdConfig.dir_cur].file_id,O_RDONLY);
    sd_file.getName(lfn,sizeof(lfn));
    sd_file.close();
    sd_dir.close();
    xSemaphoreGive(sdCardSemaphore);  // Release the semaphore
  }
  strncat(sdConfig.active_dir,lfn,sizeof(sdConfig.active_dir)-1);
  strncat(sdConfig.active_dir,"/",sizeof(sdConfig.active_dir)-1);
  sdConfig.active_dir[sizeof(sdConfig.active_dir)-1]=0;
  sdConfig.dir_cur_prev=sdConfig.dir_cur;
  sdConfig.dir_cur=0;
  // reset header scroll on directory change
  sPos[5]=0;
  scrollDir[5]=true;
  memset(scrollbuf+MAX_PATH,0,MAX_PATH);
  mlsS[5]=0;
  sUp[5]=0;
}

//not need semaphore
void browser_leave_directory(){
  memset(sdConfig.prev_dir,0,sizeof(sdConfig.prev_dir));
  for(int i=strlen(sdConfig.active_dir)-2;i>=0;i--){
    if(sdConfig.active_dir[i]=='/'){
      strncpy(sdConfig.prev_dir,&sdConfig.active_dir[i+1],sizeof(sdConfig.prev_dir)-1);
      sdConfig.active_dir[i+1]=0;
      break;
    }
  }
  sdConfig.dir_cur=sdConfig.dir_cur_prev;
  sdConfig.dir_cur_prev=0;
  // reset header scroll on directory change
  sPos[5]=0;
  scrollDir[5]=true;
  memset(scrollbuf+MAX_PATH,0,MAX_PATH);
  mlsS[5]=0;
  sUp[5]=0;
}

//semaphored
bool browser_full_path(int cur,char* path,int path_size){
  char temp[MAX_PATH]={0};
  if(cur<0||cur>=sort_list_len) return false;
  if(xSemaphoreTake(sdCardSemaphore,portMAX_DELAY)==pdTRUE){
    if(sd_dir.open(sdConfig.active_dir,O_RDONLY)){
      if(sd_file.open(&sd_dir,sort_list[cur].file_id,O_RDONLY)){
        sd_file.getName(temp,sizeof(temp));
        sd_file.close();
      }
      temp[sizeof(temp)-1]=0;
      sd_dir.close();
      strncpy(path,sdConfig.active_dir,path_size-1);
      strncat(path,temp,path_size-1);
      xSemaphoreGive(sdCardSemaphore);  // Release the semaphore
      return true;
    }
    xSemaphoreGive(sdCardSemaphore);  // Release the semaphore
  }
  path[0]=0;
  return false;
}

//semaphored
bool browser_get_played_file_name(int cur,char* path,int path_size){
  char temp[MAX_PATH]={0};
  if(cur<0||cur>=sort_list_len) return false;
  if(xSemaphoreTake(sdCardSemaphore,portMAX_DELAY)==pdTRUE){
    if(sd_play_dir.open(sdConfig.play_dir,O_RDONLY)){
      if(sd_file.open(&sd_play_dir,sort_list[cur].file_id,O_RDONLY)){
        sd_file.getName(temp,sizeof(temp));
        sd_file.close();
      }
      temp[sizeof(temp)-1]=0;
      sd_play_dir.close();
      // strncpy(path,sdConfig.play_dir,path_size-1);
      strncat(path,temp,path_size-1);
      xSemaphoreGive(sdCardSemaphore);  // Release the semaphore
      return true;
    }
    xSemaphoreGive(sdCardSemaphore);  // Release the semaphore
  }
  path[0]=0;
  return false;
}

void insertion_sort_list(){
  int i=1;
  while(i<sort_list_len){
    int j=i;
    while(j>0){
      int carry=1;
      for(int k=SORT_HASH_LEN-1;k>=0;k--){
        carry=((sort_list[j].hash[k]-sort_list[j-1].hash[k]-carry)<0)?1:0;
      }
      if(!carry) break;
      sortStruct temp;
      memcpy(&temp,&sort_list[j],sizeof(sortStruct));
      memcpy(&sort_list[j],&sort_list[j-1],sizeof(sortStruct));
      memcpy(&sort_list[j-1],&temp,sizeof(sortStruct));
      j--;
    }
    i++;
  }
  // move variable Config.dir_cur
  int file_id=-1;
  for(int i=0;i<sort_list_len;i++){
    if(sort_list[i].file_id==file_id){
      sdConfig.dir_cur=i;
      break;
    }
  }
  if(sdConfig.dir_cur<0||sdConfig.dir_cur>=sort_list_len) sdConfig.dir_cur=0;
}

int search_files_in_dir(FsFile* dir,char* found_dir,bool* found_file,const char* current_path){
  while(sd_file.openNext(dir,O_RDONLY)){
    if(!sd_file.isHidden()&&sd_file.isFile()){
      memset(lfn,0,SORT_HASH_LEN);
      sd_file.getName(lfn,sizeof(lfn));
      uint8_t file_type=browser_check_ext(lfn);
      if(file_type!=TYPE_UNK){
        if(sort_list_len>=SORT_FILES_MAX){
          sd_file.close();
          sort_list_len=0;
          printf("Too many files\nin a folder\n(%u max)\n",SORT_FILES_MAX);
          return FILE_ERR_OTHER;
        }
        sort_list[sort_list_len].file_id=sd_file.dirIndex();
        for(int i=0;i<SORT_HASH_LEN;i++){
          if(lfn[i]>='a'&&lfn[i]<='z') lfn[i]-=32; // to upper case just in case
          if(lfn[i]=='_') lfn[i]=0x20; // put underscore names to the top
          if(file_type==TYPE_AYL) lfn[i]=0x20; // put ayl on top
        }
        memcpy(sort_list[sort_list_len].hash,lfn,SORT_HASH_LEN);
        if(file_type==TYPE_AYL) cursor_offset++;
        sort_list_len++;
        if(!*found_file){
          snprintf(found_dir,512,"%s",current_path);
          *found_file=true;
        }
      }
    }else if(!sd_file.isHidden()&&sd_file.isSubDir()){
      sort_list_len++;
      cursor_offset++;
    }
    sd_file.close();
  }
  if(sort_list_len==0&&!*found_file){
    return FILE_ERR_NO_FILE;
  }
  insertion_sort_list();
  return FILE_ERR_NONE;
}

int recursive_search(FsFile* dir,char* found_dir,bool* found_file,const char* current_path){
  // Searching files into current directory first
  int result=search_files_in_dir(dir,found_dir,found_file,current_path);
  if(*found_file){
    return FILE_ERR_NONE;
  }
  // If not found supported files - entering into subfolders
  dir->rewindDirectory();
  while(sd_file.openNext(dir,O_RDONLY)){
    char fileMsg[100];
    sd_file.getName(fileMsg,sizeof(fileMsg));
    if(sd_file.isSubDir()){
      cursor_offset=0;
      sort_list_len=0;
      FsFile sub_dir;
      if(sub_dir.open(dir,fileMsg,O_RDONLY)){
        char sub_dir_path[512];
        snprintf(sub_dir_path,sizeof(sub_dir_path),"%s/%s",current_path,fileMsg);
        result=recursive_search(&sub_dir,found_dir,found_file, sub_dir_path);
        sub_dir.close();
        if(*found_file){
          return FILE_ERR_NONE;
        }
      }
    }
    sd_file.close();
  }
  return FILE_ERR_NO_FILE;
}

int browser_search_files_in_sd_dir(bool fromPlayer=false){
  memset(sort_list,0,sizeof(sort_list));
  cursor_offset=0;
  if(xSemaphoreTake(sdCardSemaphore,portMAX_DELAY)==pdTRUE){
    if(!sd_fat.begin(SD_CONFIG)){
      PlayerCTRL.isSDeject=true;
      PlayerCTRL.screen_mode=SCR_SDEJECT;
      return FILE_ERR_NO_CARD;
    }
    if(!sd_dir.open(fromPlayer?sdConfig.play_dir:sdConfig.active_dir,O_RDONLY)){
      return FILE_ERR_OTHER;
    }
    xSemaphoreGive(sdCardSemaphore); // Release the semaphore
  }
  char found_dir[512]={0};
  bool found_file=false;
  const char* initial_path=fromPlayer?sdConfig.play_dir:sdConfig.active_dir;
  snprintf(found_dir,sizeof(found_dir),"%s",initial_path);
  int result=recursive_search(&sd_dir,found_dir,&found_file,initial_path);
  sd_dir.close();
  if(result==FILE_ERR_NONE){
    // Setting up paths for Config.play_dir and Config.active_dir
    snprintf(sdConfig.play_dir,sizeof(sdConfig.play_dir),"%s",found_dir);
    snprintf(sdConfig.active_dir,sizeof(sdConfig.active_dir),"%s",found_dir);
    // Remove the extra slash at the beginning of the path, if there is one
    if(sdConfig.play_dir[0]=='/'){
      memmove(sdConfig.play_dir,sdConfig.play_dir+1,strlen(sdConfig.play_dir));
    }
    if(sdConfig.active_dir[0]=='/'){
      memmove(sdConfig.active_dir,sdConfig.active_dir+1,strlen(sdConfig.active_dir));
    }
    // Add a slash at the end of the path if there is none.
    if(sdConfig.play_dir[strlen(sdConfig.play_dir)-1]!='/'){
      strncat(sdConfig.play_dir,"/",sizeof(sdConfig.play_dir)-strlen(sdConfig.play_dir)-1);
    }
    if(sdConfig.active_dir[strlen(sdConfig.active_dir)-1]!='/'){
      strncat(sdConfig.active_dir,"/",sizeof(sdConfig.active_dir)-strlen(sdConfig.active_dir)-1);
    }
    return FILE_ERR_NONE;
  }
  PlayerCTRL.isSDeject=true;
  PlayerCTRL.screen_mode=SCR_NOFILES;
  return FILE_ERR_NO_FILE;
}

//not need semaphore
void fill_sort_hash(int idx,const char* name,uint8_t file_type,bool is_dir,uint32_t size,uint16_t date,uint16_t time){
  memset(sort_list[idx].hash,0,SORT_HASH_LEN);
  sort_list[idx].file_size=size;
  sort_list[idx].mod_date=date;
  sort_list[idx].mod_time=time;
  
  if(is_dir){
    sort_list[idx].hash[0]=1; // Directories first
    switch(sdConfig.browser_sort){
      case SORT_NAME:
      case SORT_TYPE:
      case SORT_SIZE:
        for(int i=0;i<SORT_HASH_LEN-1;i++){
          char c=name[i];
          if(c>='a'&&c<='z') c-=32;
          if(c=='_') c=0x20;
          sort_list[idx].hash[i+1]=c;
        }
        break;
      case SORT_DATE:
        sort_list[idx].hash[1]=~(date>>8);
        sort_list[idx].hash[2]=~(date&0xFF);
        sort_list[idx].hash[3]=~(time>>8);
        break;
    }
  }else if(file_type==TYPE_AYL){
    sort_list[idx].hash[0]=2; // Playlists second
    switch(sdConfig.browser_sort){
      case SORT_NAME:
      case SORT_TYPE:
      case SORT_SIZE:
        for(int i=0;i<SORT_HASH_LEN-1;i++){
          char c=name[i];
          if(c>='a'&&c<='z') c-=32;
          if(c=='_') c=0x20;
          sort_list[idx].hash[i+1]=c;
        }
        break;
      case SORT_DATE:
        sort_list[idx].hash[1]=~(date>>8);
        sort_list[idx].hash[2]=~(date&0xFF);
        sort_list[idx].hash[3]=~(time>>8);
        break;
    }
  }else{
    sort_list[idx].hash[0]=3; // Files last
    switch(sdConfig.browser_sort){
      case SORT_NAME:
        for(int i=0;i<SORT_HASH_LEN-1;i++){
          char c=name[i];
          if(c>='a'&&c<='z') c-=32;
          if(c=='_') c=0x20;
          sort_list[idx].hash[i+1]=c;
        }
        break;
      case SORT_TYPE:
        {
          const char* ext=strrchr(name,'.');
          if(ext){
            // Extension only - files within same extension keep original order
            for(int i=0;i<3&&ext[i+1];i++){
              char c=ext[i+1];
              if(c>='a'&&c<='z') c-=32;
              sort_list[idx].hash[i+1]=c;
            }
          }
        }
        break;
      case SORT_SIZE:
        sort_list[idx].hash[1]=~(size>>16);
        sort_list[idx].hash[2]=~(size>>8);
        sort_list[idx].hash[3]=~(size&0xFF);
        break;
      case SORT_DATE:
        sort_list[idx].hash[1]=~(date>>8);
        sort_list[idx].hash[2]=~(date&0xFF);
        sort_list[idx].hash[3]=~(time>>8);
        break;
    }
  }
}

//semaphored
int browser_build_list(bool fromPlayer=false){
  memset(sort_list,0,sizeof(sort_list));
  if(xSemaphoreTake(sdCardSemaphore,portMAX_DELAY)==pdTRUE){
    if(!sd_fat.begin(SD_CONFIG)){
      PlayerCTRL.isSDeject=true;
      PlayerCTRL.screen_mode=SCR_SDEJECT;
      return FILE_ERR_NO_CARD;
    }
    if(!sd_dir.open(fromPlayer?sdConfig.play_dir:sdConfig.active_dir,O_RDONLY)){
      return FILE_ERR_OTHER;
    }
    xSemaphoreGive(sdCardSemaphore);  // Release the semaphore
  }
  int file_id=-1;
  sort_list_len=0;
  cursor_offset=0;
  if(xSemaphoreTake(sdCardSemaphore,portMAX_DELAY)==pdTRUE){
    while(sd_file.openNext(&sd_dir,O_RDONLY)){
      if(!sd_file.isHidden()){
        memset(lfn,0,SORT_HASH_LEN);
        sd_file.getName(lfn,sizeof(lfn)); //full long name is needed to be able to check the extension
        uint8_t file_type=browser_check_ext(lfn);
        if(sd_file.isSubDir()||(sd_file.isFile()&&file_type!=TYPE_UNK)){
            if(sort_list_len>=SORT_FILES_MAX){
              sd_file.close();
              sd_dir.close();
              sort_list_len=0;
              char str[128];
              snprintf(str,sizeof(str),"Too many files\nin a folder\n(%u max)",SORT_FILES_MAX);
              return FILE_ERR_OTHER;
            }
            if(sd_file.isSubDir()){
              if(strcasecmp(sdConfig.prev_dir,lfn)==0) file_id=sd_file.dirIndex();
            }
            sort_list[sort_list_len].file_id=sd_file.dirIndex();
            uint32_t fsize=sd_file.isFile()?sd_file.fileSize():0;
            uint16_t fdate,ftime;
            sd_file.getModifyDateTime(&fdate,&ftime);
            fill_sort_hash(sort_list_len,lfn,file_type,sd_file.isSubDir(),fsize,fdate,ftime);
            if(sd_file.isSubDir()||file_type==TYPE_AYL) cursor_offset++;
            sort_list_len++;
        }
      }
      sd_file.close();
    }
    sd_dir.close();
    xSemaphoreGive(sdCardSemaphore);  // Release the semaphore
  }
  if(sort_list_len==0){
    return FILE_ERR_OTHER;
  }
  //now sort the list for a convenient alphanumeric ordered display
  //insertion sort
  int i=1;
  while(i<sort_list_len){
    int j=i;
    while(j>0){
      int carry=1;
      for(int k=SORT_HASH_LEN-1;k>=0;k--){
        carry=((sort_list[j].hash[k]-sort_list[j-1].hash[k]-carry)<0)?1:0;
      }
      if (!carry) break;
      sortStruct temp;
      memcpy(&temp,&sort_list[j],sizeof(sortStruct));
      memcpy(&sort_list[j],&sort_list[j-1],sizeof(sortStruct));
      memcpy(&sort_list[j-1],&temp,sizeof(sortStruct));
      j--;
    }
    i++;
  }
  //or bubblesort
  /*
    for(int i=0;i<sort_list_len-1;i++){
      for(int j=0;j<sort_list_len-i-1;j++){
        //if arr j > arr j+1 swap
        int carry=1;
        for(int k=SORT_HASH_LEN-1;k>=0;k++){
          carry=((sort_list[j].hash[k]-sort_list[j+1].hash[k]-carry)<0)?1:0;
        }
        if(!carry){
          sortStruct temp;
          memcpy(&temp,&sort_list[j],sizeof(sortStruct));
          memcpy(&sort_list[j],&sort_list[j+1],sizeof(sortStruct));
          memcpy(&sort_list[j+1],&temp,sizeof(sortStruct));
        }
      }
    }
  */
  for(int i=0;i<sort_list_len;i++){
    if(sort_list[i].file_id==file_id){
      sdConfig.dir_cur=i;
      break;
    }
  }
  if(sdConfig.dir_cur<0||sdConfig.dir_cur>=sort_list_len) sdConfig.dir_cur=0;
  return FILE_ERR_NONE;
}

//not need semaphore
bool browser_move_cur(int dir,bool loop){
  bool done=false;
  sdConfig.dir_cur+=dir;
  if(loop){
    if(sdConfig.dir_cur<0) sdConfig.dir_cur=sort_list_len-1;
    if(sdConfig.dir_cur>=sort_list_len) sdConfig.dir_cur=0;
  }else{
    if(sdConfig.dir_cur<0){
      sdConfig.dir_cur=0;
      done=true;
    }
    if(sdConfig.dir_cur>=sort_list_len){
      sdConfig.dir_cur=sort_list_len-1;
      done=true;
    }
  }
  // reset only file scroll (index 0), keep header scroll (index 5)
  sPos[0]=0;
  scrollDir[0]=true;
  memset(scrollbuf,0,MAX_PATH);
  mlsS[0]=0;
  return done;
}

//not need semaphore
void browser_shuffle_cur(){
  int prev_cur=sdConfig.dir_cur;
  while(1){
    sdConfig.dir_cur=rand()%sort_list_len;
    if(sdConfig.dir_cur!=prev_cur) break;
    yield();
  }
}

//semaphored
void browser_dir_draw_begin(int id){
  if(xSemaphoreTake(sdCardSemaphore,portMAX_DELAY)==pdTRUE){
    sd_dir.open(sdConfig.active_dir,O_RDONLY);
    xSemaphoreGive(sdCardSemaphore);  // Release the semaphore
  }
}

//semaphored
void browser_dir_draw_item(int sx,int sy,int id,bool drawCursor){
  char tmp[MAX_PATH];
  memcpy(tmp,sdConfig.active_dir,sizeof(sdConfig.active_dir));
  if(xSemaphoreTake(sdCardSemaphore,portMAX_DELAY)==pdTRUE){
    sd_file.open(&sd_dir,sort_list[id].file_id,O_RDONLY);
    sd_file.getName(lfn,sizeof(lfn));
    sd_file.close();
    xSemaphoreGive(sdCardSemaphore);  // Release the semaphore
  }
  lfn[sizeof(lfn)-1]=0;
  uint8_t type=MUS;
  if(sort_list[id].hash[0]==1) type=DIR;
  if(browser_check_ext(lfn)==TYPE_AYL) type=AYL;
  char buf[MAX_PATH];
  if(drawCursor){
    // draw cursor
    img.fillRoundRect(0,0,img.width(),8*2,3,BRWSR_CURSOR);
  }
  switch(type){
    case MUS:
      if(!strcmp(sdConfig.active_dir,sdConfig.play_dir)&&sdConfig.play_cur==id&&!sdConfig.isPlayAYL){
        spr_print(img,sx,sy,lfn,2,BRWSR_PLAY_FILE);  // playing file
      }else{
        spr_print(img,sx,sy,lfn,2,get_file_type_color(lfn)); // mus files types
      }
      break;
    case DIR:
      sprintf(buf,"[%s]",lfn);
      strcat(tmp,lfn);
      strcat(tmp,"/");
      // Processing and highlighting full playing path folders\file or playlist
      if(strstr(sdConfig.play_dir,tmp)!=NULL&&!sdConfig.isPlayAYL){
        spr_print(img,sx,sy,buf,2,BRWSR_PLAY_DIR);  // dir playing color
      }else if(strstr(sdConfig.play_ayl_file,tmp)!=NULL&&sdConfig.isPlayAYL){
        spr_print(img,sx,sy,buf,2,BRWSR_PLAY_PLST);  // playlist playing color
      }else{
        spr_print(img,sx,sy,buf,2,BRWSR_DIR);  // dir color
      }
      break;
    case AYL:
      sprintf(buf,"<%s>",lfn);
      strcat(tmp,lfn);
      if(!strcmp(sdConfig.play_ayl_file,tmp)&&sdConfig.isPlayAYL){
        spr_print(img,sx,sy,buf,2,BRWSR_PLAY_PLST);  // playlist playing color
      }else{
        spr_print(img,sx,sy,buf,2,BRWSR_PLST);
      }
      break;
  }
}

//semaphored
void browser_dir_draw_end(){
  if(xSemaphoreTake(sdCardSemaphore,portMAX_DELAY)==pdTRUE){
    sd_dir.close();
    xSemaphoreGive(sdCardSemaphore);  // Release the semaphore
  }
}

//in playlist.h
void browser_ayl_draw_begin(int id){
  playlist_open(sdConfig.ayl_file,id);
}

//in playlist.h
void browser_ayl_draw_item(int sx,int sy,int id,bool drawCursor){
  playlist_iterate(lfn,sizeof(lfn));
  playlist_file_name(lfn,sizeof(lfn));
  if(drawCursor){
    // draw cursor
    img.fillRoundRect(0,0,img.width(),8*2,3,BRWSR_CURSOR);
  }
  if(!strcmp(sdConfig.ayl_file,sdConfig.play_ayl_file)&&sdConfig.play_cur==id&&sdConfig.isPlayAYL){
    spr_print(img,sx,sy,lfn,2,TFT_BLUE);
  }else{
    spr_print(img,sx,sy,lfn,2,WILD_CYAN_D2);
  }
}

//in playlist.h
void browser_ayl_draw_end(){
  playlist_close();
}

int browser_screen(int mode){
  PGM_P header_dir=PSTR("Files");
  PGM_P header_ayl=PSTR("Playlist");
  if(mode==BROWSE_DIR){
    if(browser_rebuild){
      browser_rebuild=0;
      int ret=browser_build_list();
      if(ret!=FILE_ERR_NONE){
        if(ret!=FILE_ERR_NO_CARD){
          browser_leave_directory();
        }else{
          browser_reset_directory();
        }
        browser_rebuild=1;
        return ret;
      }
    }
  }else{
    if(browser_rebuild){
      browser_rebuild=0;
      if(!playlist_open(sdConfig.ayl_file,0)) return FILE_ERR_NO_CARD;
      sort_list_len=0;
      while(playlist_iterate(lfn,sizeof(lfn))){
        sort_list_len++;
      }
      playlist_close();
    }
  }
  if(PlayerCTRL.scr_mode_update[SCR_BROWSER]){ 
    int id=sdConfig.dir_cur-BROWSER_LINES/2;
    if(id>=sort_list_len-BROWSER_LINES) id=sort_list_len-BROWSER_LINES;
    if(id<0) id=0;
    img.setColorDepth(8);
    img.createSprite(224,16);
    img.setTextWrap(false);
    img.setTextColor(TFT_WHITE);
    img.setTextSize(2);
    img.setFreeFont(&WildFont);
    //draw header
    // PGM_P header_str=(mode==BROWSE_DIR)?header_dir:header_ayl;
    // spr_println(img,0,1,header_str,2,ALIGN_CENTER,WILD_CYAN);
    PGM_P header_str=(mode==BROWSE_DIR)?(strcmp(sdConfig.active_dir,"/")==0?"Root":sdConfig.active_dir):sdConfig.ayl_file;
    char sort_stub[8];
    if(mode==BROWSE_DIR) snprintf(sort_stub,sizeof(sort_stub),"|%s",sort_names[sdConfig.browser_sort]);
    int sort_stub_width=(mode==BROWSE_DIR)?tft_strlen(sort_stub,2):0;
    int header_width=tft_strlen(header_str,2);
    img.fillScreen(0);
    img.fillRect(0,0,img.width(),8*2,BRWSR_HEADER_BG);
    if(header_width+sort_stub_width>img.width()){
      // header path is too long - enable scrolling
      char header_buf[MAX_PATH];
      strncpy(header_buf,header_str,sizeof(header_buf)-1);
      header_buf[sizeof(header_buf)-1]=0;
      memcpy(scrollbuf+MAX_PATH,header_buf,sizeof(header_buf));
      if(sUp[5]==0){
        sUp[5]=S_UPD5;
        mlsS[5]=0;
      }
      if(mode==BROWSE_DIR) spr_print(img,img.width()-sort_stub_width,8*2,sort_stub,2,BRWSR_SORT);
    }else{
      // header fits - draw normally
      spr_print(img,0,8*2,header_str,2,BRWSR_HEADER_TX);
      if(mode==BROWSE_DIR) spr_print(img,img.width()-sort_stub_width,8*2,sort_stub,2,BRWSR_SORT);
      sUp[5]=0;
      mlsS[5]=0;
    }
    if(sUp[5]==0){
      img.pushSprite(8,8);
    }

    int sx=0;
    int sy=8*2;
    int screenY=8+8*2;
    if(mode==BROWSE_DIR){
      browser_dir_draw_begin(id);
    }else{
      browser_ayl_draw_begin(id);
    }
    for(int i=0;i<BROWSER_LINES;i++){
      img.fillScreen(0);
      if(id>=0&&id<sort_list_len){
        if(mode==BROWSE_DIR){
          browser_dir_draw_item(sx,sy,id,sdConfig.dir_cur==id);
        }else{
          browser_ayl_draw_item(sx,sy,id,sdConfig.dir_cur==id);
        }
        if(sdConfig.dir_cur==id){
          if(tft_strlen(lfn,2)>img.width()){
            memcpy(scrollbuf,lfn,sizeof(lfn));
            sUp[0]=S_UPD_DIR;
            mlsS[0]=millis();
            scroll=true;
            scrollSY=screenY;
          }else{
            sPos[0]=0;
            scrollDir[0]=true;
            memset(scrollbuf,0,MAX_PATH);
            mlsS[0]=0;
            scroll=false;
            scrollSY=0;
          }
        }
      }
      img.pushSprite(8,screenY);
      screenY+=8*2;
      id++;
    }
    if(mode==BROWSE_DIR){
      browser_dir_draw_end();
    }else{
      browser_ayl_draw_end();
    }
    // scrollbar
    if(sort_list_len>BROWSER_LINES){
      // draw scrollbar
      draw_scrollbar(sdConfig.dir_cur,sort_list_len);
    }else{
      // clear scrollbar
      clear_scrollbar();
    }
    PlayerCTRL.scr_mode_update[SCR_BROWSER]=false;
    img.deleteSprite();
  }
  //scroll header
  if(sUp[5]>0){
    char sort_stub[8];
    if(mode==BROWSE_DIR) snprintf(sort_stub,sizeof(sort_stub),"|%s",sort_names[sdConfig.browser_sort]);
    int sort_stub_width=(mode==BROWSE_DIR)?tft_strlen(sort_stub,2):0;
    scrollString(scrollbuf+MAX_PATH,2,BRWSR_HEADER_TX,224-sort_stub_width,16,8,8,5,BRWSR_HEADER_BG,false);
    // draw sort stub on top of scrolled header
    if(mode==BROWSE_DIR){
      img.setColorDepth(8);
      img.createSprite(sort_stub_width,16);
      img.fillScreen(BRWSR_HEADER_BG);
      img.setFreeFont(&WildFont);
      img.setTextSize(2);
      img.setTextWrap(false);
      img.setTextColor(BRWSR_SORT);
      spr_print(img,0,8*2,sort_stub,2,BRWSR_SORT);
      img.pushSprite(8+224-sort_stub_width,8);
      img.deleteSprite();
    }
  }
  //scroll
  if(scroll){
    if(sdConfig.isPlayAYL){ // in playlist
      if(!strcmp(sdConfig.ayl_file,sdConfig.play_ayl_file)&&sdConfig.play_cur==sdConfig.dir_cur){
        scrollString(scrollbuf,2,BRWSR_PLAY_FILE,224,16,8,scrollSY,0); // playing file in playlist
      }else{
        scrollString(scrollbuf,2,get_file_type_color(scrollbuf),224,16,8,scrollSY,0); // file in playlist under cursor
      }
    }else{  // in folder
      if(!strcmp(sdConfig.active_dir,sdConfig.play_dir)&&sdConfig.play_cur==sdConfig.dir_cur){
        scrollString(scrollbuf,2,BRWSR_PLAY_FILE,224,16,8,scrollSY,0); // playing file
      }else{
        scrollString(scrollbuf,2,get_file_type_color(scrollbuf),224,16,8,scrollSY,0); // file in folder under cursor
      }
    }
  }
  //keypad survey
  if(up.hasClicks(1)&&mode==BROWSE_DIR&&lcdBlackout==false&&scrNotPlayer==false){
    // Save current cursor file_id
    uint16_t cursor_file_id=sort_list[sdConfig.dir_cur].file_id;
    sdConfig.browser_sort++;
    if(sdConfig.browser_sort>=SORT_ALL) sdConfig.browser_sort=SORT_NAME;
    browser_rebuild=1;
    PlayerCTRL.scr_mode_update[SCR_BROWSER]=true;
    // Rebuild list with new sort
    browser_build_list();
    // Find new position of cursor file
    for(int i=0;i<sort_list_len;i++){
      if(sort_list[i].file_id==cursor_file_id){
        sdConfig.dir_cur=i;
        break;
      }
    }
    // Update playing file position if in playing directory
    if(!strcmp(sdConfig.active_dir,sdConfig.play_dir)&&!sdConfig.isPlayAYL){
      uint16_t play_file_id=sort_list_play[sdConfig.play_cur].file_id;
      // Find new position of playing file
      for(int i=0;i<sort_list_len;i++){
        if(sort_list[i].file_id==play_file_id){
          sdConfig.play_cur=i;
          break;
        }
      }
      memcpy(sort_list_play,sort_list,sizeof(sort_list));
      sdConfig.play_cur_start=cursor_offset;
    }
    browser_rebuild=0;
  }
  if(enc.left()&&lcdBlackout==false&&scrNotPlayer==false){
    PlayerCTRL.scr_mode_update[SCR_BROWSER]=true;
    if(enc.fast()) browser_move_cur(-5,true);
    else browser_move_cur(-1,true);
    enc.clear();
  }
  if(enc.right()&&lcdBlackout==false&&scrNotPlayer==false){
    PlayerCTRL.scr_mode_update[SCR_BROWSER]=true;
    if(enc.fast()) browser_move_cur(5,true);
    else browser_move_cur(1,true);
    enc.clear();
  }
  if(enc.hasClicks(1)&&!up.holding()&&lcdBlackout==false&&scrNotPlayer==false){
    if(mode==BROWSE_DIR){
      if(sort_list[sdConfig.dir_cur].hash[0]==1){ //directory
        browser_enter_directory();
        PlayerCTRL.scr_mode_update[SCR_BROWSER]=true;
        browser_rebuild=1;
      }else{ //file
        browser_full_path(sdConfig.dir_cur,lfn,sizeof(lfn));
        switch(browser_check_ext(lfn)){
          case TYPE_UNK:
            return FILE_ERR_UNK_FORMAT;
            break;
          case TYPE_AYL: //enter playlist mode
            strncpy(sdConfig.ayl_file,lfn,sizeof(sdConfig.ayl_file)-1);
            sdConfig.dir_cur_prev=sdConfig.dir_cur;
            sdConfig.dir_cur=0;
            PlayerCTRL.scr_mode_update[SCR_BROWSER]=true;
            browser_rebuild=1;
            sdConfig.isBrowserPlaylist=BROWSE_AYL;
            vTaskDelay(pdMS_TO_TICKS(30));
            break;
          case TYPE_PT1:
          case TYPE_PT2:
          case TYPE_PT3:
          case TYPE_STC:
          case TYPE_STP:
          case TYPE_ASC:
          case TYPE_PSC:
          case TYPE_SQT:
          case TYPE_AY:
          case TYPE_PSG:
          case TYPE_RSF:
          case TYPE_YRG:
          case TYPE_MOD:
          case TYPE_S3M:
        #if defined(CONFIG_IDF_TARGET_ESP32S3)
          case TYPE_XM:
        #endif
          case TYPE_TAP:
          case TYPE_TZX:
          case TYPE_MP3:
          case TYPE_WAV:
            muteAmp();
            muteAYBeep();
            memcpy(sdConfig.play_dir,sdConfig.active_dir,sizeof(sdConfig.active_dir));
            memcpy(sort_list_play,sort_list,sizeof(sort_list));
            sdConfig.play_count_files=sort_list_len;
            sdConfig.play_cur_start=cursor_offset;
            sdConfig.play_cur=sdConfig.dir_cur;
            // leave AYL play
            sdConfig.play_ayl_file[0]=0;
            sdConfig.isPlayAYL=false;
            // rebuild browser list command
            browser_rebuild=1;
            PlayerCTRL.scr_mode_update[SCR_BROWSER]=true;
            // change track command
            PlayerCTRL.isBrowserCommand=true;
            PlayerCTRL.autoPlay=false;
            PlayerCTRL.isFinish=true;
            vTaskDelay(pdMS_TO_TICKS(30));
            break;
        }
      }
    }else{
      muteAmp();
      muteAYBeep();
      PlayerCTRL.isPlay=false;
      playlist_get_entry_full_path(sdConfig.dir_cur,lfn,sizeof(lfn));
      memcpy(sdConfig.play_ayl_file,sdConfig.ayl_file,sizeof(sdConfig.ayl_file));
      sdConfig.play_cur=sdConfig.dir_cur;
      // enter AYL play
      sdConfig.play_count_files=sort_list_len;
      sdConfig.play_cur_start=0;
      sdConfig.isPlayAYL=true;
      // rebuild browser list command
      browser_rebuild=1;
      PlayerCTRL.scr_mode_update[SCR_BROWSER]=true;
      // change track command
      PlayerCTRL.isBrowserCommand=true;
      PlayerCTRL.autoPlay=false;
      PlayerCTRL.isFinish=true;
      vTaskDelay(pdMS_TO_TICKS(30));
    }
    sd_config_save();
    return sdConfig.dir_cur;
  }
  if(up.holding()&&enc.hasClicks(1)&&mode==BROWSE_DIR&&sort_list[sdConfig.dir_cur].hash[0]!=1&&lcdBlackout==false&&scrNotPlayer==false){ // Remove file if not folder and not in playlist
    char pf[MAX_PATH];
    char rf[MAX_PATH];
    sdConfig.play_ayl_file[0]=0; // clean string
    browser_full_path(sdConfig.dir_cur,rf,sizeof(rf)); // Get full removed file path
    browser_get_played_file_name(sdConfig.play_cur,sdConfig.play_ayl_file,sizeof(sdConfig.play_ayl_file));
    strncpy(pf,sdConfig.play_dir,sizeof(pf)-1);
    strncat(pf,sdConfig.play_ayl_file,sizeof(pf)-1);
    if(!strcmp(rf,pf)){ // if played file
      if(sdConfig.play_count_files>1){
        PlayerCTRL.isPlay=false;
        if(xSemaphoreTake(sdCardSemaphore,portMAX_DELAY)==pdTRUE){
          sd_fat.remove(rf);
          xSemaphoreGive(sdCardSemaphore);  // Release the semaphore
        }
        // update folder
        browser_build_list();
        memcpy(sdConfig.play_dir,sdConfig.active_dir,sizeof(sdConfig.active_dir));
        memcpy(sort_list_play,sort_list,sizeof(sort_list));
        sdConfig.play_count_files=sort_list_len;
        if(sdConfig.play_count_files==0&&strcmp(sdConfig.play_dir,"/")){ // if not root directory
          browser_leave_directory();
          browser_build_list();
          memcpy(sdConfig.play_dir,sdConfig.active_dir,sizeof(sdConfig.active_dir));
          memcpy(sort_list_play,sort_list,sizeof(sort_list));
          sdConfig.play_count_files=sort_list_len;
          if(sdConfig.play_count_files==0) goto pf0;
        }
        sdConfig.play_cur_start=cursor_offset;
        sdConfig.play_prev_cur=sdConfig.play_cur;
        sdConfig.play_cur=sdConfig.dir_cur;
        sdConfig.isPlayAYL=false;
        // change track command
        PlayerCTRL.isBrowserCommand=true;
        PlayerCTRL.autoPlay=false;
        PlayerCTRL.isFinish=true;
        // rebuild browser list command
        browser_rebuild=1;
        PlayerCTRL.scr_mode_update[SCR_BROWSER]=true;
        vTaskDelay(pdMS_TO_TICKS(30));
      }else{ // no more file in this dir - leave, search new
        PlayerCTRL.isPlay=false;
        if(xSemaphoreTake(sdCardSemaphore,portMAX_DELAY)==pdTRUE){
          sd_fat.remove(rf);
          xSemaphoreGive(sdCardSemaphore);  // Release the semaphore
        }
      pf0:
        // reseting
        configResetPlayingPath();
        sort_list_len=0;
        sdConfig.play_count_files=sort_list_len;
        sdConfig.play_cur_start=0;
        sort_list_len=0;
        // now prepare default playing file
        browser_search_files_in_sd_dir(true);
        memcpy(sort_list_play,sort_list,sizeof(sort_list));
        sdConfig.play_count_files=sort_list_len;
        sdConfig.play_cur_start=cursor_offset;
        sdConfig.play_cur=sdConfig.dir_cur=cursor_offset;
        sdConfig.isPlayAYL=false;
        // change track command
        PlayerCTRL.isBrowserCommand=true;
        PlayerCTRL.autoPlay=false;
        PlayerCTRL.isFinish=true;
        // rebuild browser list command
        browser_rebuild=1;
        PlayerCTRL.scr_mode_update[SCR_BROWSER]=true;
      }
    }else if(!strcmp(sdConfig.play_dir,sdConfig.active_dir)&&strcmp(rf,pf)){ // if in playing dir
      if(sdConfig.play_count_files>1){
        if(xSemaphoreTake(sdCardSemaphore,portMAX_DELAY)==pdTRUE){
          sd_fat.remove(rf);
          xSemaphoreGive(sdCardSemaphore);  // Release the semaphore
        }
        // update folder
        browser_build_list();
        memcpy(sdConfig.play_dir,sdConfig.active_dir,sizeof(sdConfig.active_dir));
        memcpy(sort_list_play,sort_list,sizeof(sort_list));
        sdConfig.play_count_files=sort_list_len;
        sdConfig.play_cur_start=cursor_offset;
        if(sdConfig.play_cur>sdConfig.dir_cur+sdConfig.play_cur_start) sdConfig.play_cur--; // if removed file before playing file fix
        sdConfig.isPlayAYL=false;
        // rebuild browser list command
        browser_rebuild=1;
        PlayerCTRL.scr_mode_update[SCR_BROWSER]=true;
      }else{ // no more file in this dir - leave, search new
        PlayerCTRL.isPlay=false;
        if(xSemaphoreTake(sdCardSemaphore,portMAX_DELAY)==pdTRUE){
          sd_fat.remove(rf);
          xSemaphoreGive(sdCardSemaphore);  // Release the semaphore
        }
        // reseting
        configResetPlayingPath();
        sort_list_len=0;
        sdConfig.play_count_files=sort_list_len;
        sdConfig.play_cur_start=0;
        sort_list_len=0;
        // now prepare default playing file
        browser_search_files_in_sd_dir(true);
        memcpy(sort_list_play,sort_list,sizeof(sort_list));
        sdConfig.play_count_files=sort_list_len;
        sdConfig.play_cur_start=cursor_offset;
        sdConfig.play_cur=sdConfig.dir_cur=cursor_offset;
        sdConfig.isPlayAYL=false;
        // change track command
        PlayerCTRL.isBrowserCommand=true;
        PlayerCTRL.autoPlay=false;
        PlayerCTRL.isFinish=true;
        // rebuild browser list command
        browser_rebuild=1;
        PlayerCTRL.scr_mode_update[SCR_BROWSER]=true;
      }
    }else{ // not played dir
      if(xSemaphoreTake(sdCardSemaphore,portMAX_DELAY)==pdTRUE){
        sd_fat.remove(rf);
        xSemaphoreGive(sdCardSemaphore);  // Release the semaphore
      }
      browser_rebuild=1;
      PlayerCTRL.scr_mode_update[SCR_BROWSER]=true;
    }
    sd_config_save();
    return sdConfig.dir_cur;
  }
  if(dn.click()&&lcdBlackout==false&&scrNotPlayer==false){
    if(mode==BROWSE_DIR){
      browser_leave_directory();
      PlayerCTRL.scr_mode_update[SCR_BROWSER]=true;
      browser_rebuild=1;
    }else{ // leave playlist
      sdConfig.dir_cur=sdConfig.dir_cur_prev;
      sdConfig.dir_cur_prev=0;
      sdConfig.ayl_file[0]=0;
      PlayerCTRL.scr_mode_update[SCR_BROWSER]=true;
      browser_rebuild=1;
      sdConfig.isBrowserPlaylist=BROWSE_DIR;
    }
    sd_config_save();
    return sdConfig.dir_cur;
  }
  keysTimeOut();
  return 0;
}

void initSemaphore(){
  sdCardSemaphore=xSemaphoreCreateMutex();
  if(sdCardSemaphore==NULL){
    printf("Error creating sd semaphore\n");
  }else{
    // Give the semaphore so it's available for the first take
    xSemaphoreGive(sdCardSemaphore);
  }
  outSemaphore=xSemaphoreCreateBinary();
  if(outSemaphore==NULL){
    printf("Failed to create outSemaphore\n");
  }else{
    // Give the semaphore so it's available for the first take
    xSemaphoreGive(outSemaphore);
  }
}
