djspawnbrest/ESP32AY/src/player.h

static bool dynRebuild=true;
static bool clockShowFlag=true;
static bool colCh2=false;
int ay_cur_song=0;
int tap_cur_block=0;
int tzx_cur_block=0;
int tap_total_blocks=0;
int tzx_total_blocks=0;
char blockTypeLabel[16] = "Author";
uint16_t prev_file_id=0;

TaskHandle_t ayPlayTaskHandle=NULL;

void player_shuffle_cur(){
  int prev_cur=sdConfig.play_cur;
  if(sdConfig.play_count_files<=0) return;
  while(1){
    // randomSeed(analogRead(VOLTPIN));
    sdConfig.play_cur=random(sdConfig.play_cur_start,sdConfig.play_count_files);
    if(sdConfig.play_cur!=prev_cur) break;
    yield();
  }
}

void muteAYBeep(){
  sound_clear_buf();
  for(uint8_t chip=0;chip<2;chip++){
    ay_write(chip,0x07,0xff);
    ay_write(chip,0x08,0x00);
    ay_write(chip,0x09,0x00);
    ay_write(chip,0x0a,0x00);
  }
}

//semaphored; subsong is only used for AY format
int music_open(const char* filename,int ay_sub_song){
  int err=FILE_ERR_OTHER;
  if(xSemaphoreTake(sdCardSemaphore,portMAX_DELAY)==pdTRUE){
    if(!sd_fat.begin(SD_CONFIG)) return FILE_ERR_NO_CARD;
    if(sd_play_file.open(filename,O_RDONLY)){
      sd_play_file.getName(lfn,sizeof(lfn));
      memcpy(playedFileName,lfn,sizeof(lfn));
      PlayerCTRL.music_type=browser_check_ext(lfn);
      unsigned long beforeLoading=millis();
      switch(PlayerCTRL.music_type){
        case TYPE_UNK: break;
        case TYPE_AYL: break;
        case TYPE_PT1:
        case TYPE_PT2:
        case TYPE_PT3:
        case TYPE_STC:
        case TYPE_STP:
        case TYPE_ASC:
        case TYPE_PSC:
        case TYPE_SQT:
          memset(&AYInfo,0,sizeof(AYInfo));
          music_data_size=sd_play_file.fileSize();
          if(music_data_size<=sizeof(music_data)){
            sd_play_file.read((char*)music_data,music_data_size);
            err=FILE_ERR_NONE;
          }else{
            err=FILE_ERR_TOO_LARGE;
          }
          sd_play_file.close();
          break;
        case TYPE_AY:
          memset(&AYInfo,0,sizeof(AYInfo));
          err=AY_Load(AYInfo,ay_sub_song); //uses currently opened file stream
          sd_play_file.close();
          break;
        case TYPE_PSG:
          memset(&music_data,0,sizeof(music_data));
          music_data_size=sd_play_file.fileSize();
          memset(&AYInfo,0,sizeof(AYInfo));
          AYInfo.Length=0;
          AYInfo.Loop=0;
          // sd_play_file.read(fileInfoBuf,16);
          // memcpy(&AYInfo.Length,&fileInfoBuf[8],sizeof(unsigned long));
          //check if present frames count info else calculate and write to file
          if(AYInfo.Length==0){
            sd_play_file.close();
            sd_play_file.open(filename, O_RDWR);
            bool fe=false;
            bool rd=true;
            while(sd_play_file.available()&&rd){
              byte b=sd_play_file.read();
              switch(b){
                case 0xFF:
                  AYInfo.Length++;
                  break;
                case 0xFE:
                  fe=true;
                  break;
                case 0xFD:
                  rd=false;
                  break;
                default:
                  if(fe){AYInfo.Length+=b*4-1;fe=false;break;}
                  if(b<0xFC) sd_play_file.seekCur(1);
                  break;
              }
            }
            sd_play_file.rewind();
            sd_play_file.read(fileInfoBuf,8);
            sd_play_file.write(&AYInfo.Length,sizeof(AYInfo.Length));
            sd_play_file.close();
            sd_play_file.open(filename, O_RDONLY);
          }
          sd_play_file.rewind();
          //skip 16 info bytes
          sd_play_file.seekSet(16);
          memcpy(&AYInfo.Name,utf8rus(playedFileName),utf8_strlen(playedFileName)-4);
          fillBuffer();
          err=FILE_ERR_NONE;
          break;
        case TYPE_RSF:
          memset(&music_data,0,sizeof(music_data));
          music_data_size=sd_play_file.fileSize();
          memset(&AYInfo,0,sizeof(AYInfo));
          uint16_t freq,offset,loop;
          if(sd_play_file.read(fileInfoBuf,4)<=0)break; // short file
          switch(fileInfoBuf[3]){ // reading RSF HEADER v3 only supported!
            case 3: // RSF ver.3
              if(sd_play_file.read(fileInfoBuf,14)==0)break; // short file
              memcpy(&freq,&fileInfoBuf[0],sizeof(uint16_t));
              memcpy(&offset,&fileInfoBuf[2],sizeof(uint16_t));
              memcpy(&AYInfo.Length,&fileInfoBuf[4],sizeof(uint32_t));
              memcpy(&AYInfo.Loop,&fileInfoBuf[8],sizeof(uint32_t));
              AYInfo.Loop=0;
              sd_play_file.rewind();
              sd_play_file.seekSet(20);
              if(sd_play_file.read(fileInfoBuf,offset-20)==0)break; // short file
              uint16_t offsetString=0; //20 -start position for strings - name, author, comment
              uint8_t offsetBuf[4];
              uint16_t bufPos = 0;
              offsetBuf[bufPos]=0;
              while(offsetString<=offset-21){
                if(fileInfoBuf[offsetString]==0x00){
                  bufPos++;
                  offsetBuf[bufPos]=offsetString+1;
                }
                offsetString++;
              }
              memcpy(&AYInfo.Name,&fileInfoBuf[offsetBuf[0]],offsetBuf[1]);
              memcpy(&AYInfo.Author,&fileInfoBuf[offsetBuf[1]],offsetBuf[2]-offsetBuf[1]);
              break;
          }
          sd_play_file.rewind();
          sd_play_file.seekSet(offset);
          fillBuffer();
          err=FILE_ERR_NONE;
          break;
        case TYPE_YRG:
          yrgFrame=0;
          memset(&music_data,0,sizeof(music_data));
          music_data_size=sd_play_file.fileSize();
          memset(&AYInfo,0,sizeof(AYInfo));
          AYInfo.Loop=0;
          AYInfo.Length=(unsigned long)(music_data_size/16);
          memcpy(&AYInfo.Name,utf8rus(playedFileName),utf8_strlen(playedFileName)-4);
          fillBuffer();
          err=FILE_ERR_NONE;
          break;
        case TYPE_MOD:
          sd_play_file.close();
          xSemaphoreGive(sdCardSemaphore);  // Release the semaphore we no need for AudioFileSourceSDFAT
          memset(&music_data,0,sizeof(music_data));
          memset(&AYInfo,0,sizeof(AYInfo));
          MOD_GetInfo(filename);
          break;
        case TYPE_S3M:
          sd_play_file.close();
          xSemaphoreGive(sdCardSemaphore);  // Release the semaphore we no need for AudioFileSourceSDFAT
          memset(&music_data,0,sizeof(music_data));
          memset(&AYInfo,0,sizeof(AYInfo));
          S3M_GetInfo(filename);
          break;
      #if defined(CONFIG_IDF_TARGET_ESP32S3)
        case TYPE_XM:
          sd_play_file.close();
          xSemaphoreGive(sdCardSemaphore);  // Release the semaphore we no need for AudioFileSourceSDFAT
          memset(&music_data,0,sizeof(music_data));
          memset(&AYInfo,0,sizeof(AYInfo));
          XM_GetInfo(filename);
          break;
      #endif
        case TYPE_TAP:
          sd_play_file.close();
          xSemaphoreGive(sdCardSemaphore);  // Release the semaphore we no need for AudioFileSourceSDFAT
          memset(&music_data,0,sizeof(music_data));
          memset(&AYInfo,0,sizeof(AYInfo));
          TAP_GetInfo(filename);
          break;
        case TYPE_TZX:
          sd_play_file.close();
          xSemaphoreGive(sdCardSemaphore);  // Release the semaphore we no need for AudioFileSourceSDFAT
          memset(&music_data,0,sizeof(music_data));
          memset(&AYInfo,0,sizeof(AYInfo));
          TZX_GetInfo(filename);
          break;
        case TYPE_MP3:
          sd_play_file.close();
          xSemaphoreGive(sdCardSemaphore);  // Release the semaphore we no need for AudioFileSourceSDFAT
          memset(&music_data,0,sizeof(music_data));
          memset(&AYInfo,0,sizeof(AYInfo));
          MP3_GetInfo(filename);
          break;
        case TYPE_WAV:
          sd_play_file.close();
          xSemaphoreGive(sdCardSemaphore);  // Release the semaphore we no need for AudioFileSourceSDFAT
          memset(&music_data,0,sizeof(music_data));
          memset(&AYInfo,0,sizeof(AYInfo));
          WAV_GetInfo(filename);
          break;
      }
      loadingTime=millis()-beforeLoading;
    }
    xSemaphoreGive(sdCardSemaphore);  // Release the semaphore
  }
  #ifdef DEBUG_RAM
    printf("Music opened!\n");
    checkHeap();
  #endif
  return err;
}

bool player_full_path(int cur, char* path, int path_size){
  char temp[MAX_PATH]={0};
  if(cur<0||cur>=sdConfig.play_count_files) return false;
  if(sd_play_dir.open(sdConfig.play_dir,O_RDONLY)){
    if(sd_play_file.open(&sd_play_dir,sort_list_play[cur].file_id,O_RDONLY)){
      sd_play_file.getName(temp,sizeof(temp));
      sd_play_file.close();
    }
    temp[sizeof(temp)-1]=0;
    sd_play_dir.close();
    strncpy(path,sdConfig.play_dir,path_size-1);
    strncat(path,temp,path_size-1);
    return true;
  }
  path[0]=0;
  return false;
}

int checkSDonStart(){
  muteAmp();
  frame_cnt=0;
  frame_max=frameMax(PLAY_NORMAL);
  int err=FILE_ERR_OTHER;
  while(!sd_fat.begin(SD_CONFIG)){ // while
    sdEject();
  }
  PlayerCTRL.screen_mode=SCR_PLAYER;
  PlayerCTRL.isSDeject=false;
  if(sdConfig.isPlayAYL){ // check if last played playlist exists
    if(sd_play_dir.open(sdConfig.play_ayl_file,O_RDONLY)){
      sd_play_dir.close();
      if(!playlist_open(sdConfig.ayl_file,0,true)) return FILE_ERR_NO_CARD;
      sort_list_len=0;
      while(playlist_iterate(lfn,sizeof(lfn),true)){
        sort_list_len++;
      }
      playlist_close();
      sdConfig.play_count_files=sort_list_len;
      sdConfig.play_cur_start=0;
      sort_list_len=0;
      memcpy(sort_list_play,sort_list,sizeof(sort_list));
      playlist_get_entry_full_path(sdConfig.play_cur,lfn,sizeof(lfn),true);
      if(sd_play_file.open(lfn,O_RDONLY)){
        sd_play_file.close();
        //now prepare playing file
        PlayerCTRL.autoPlay=false;
        PlayerCTRL.isBrowserCommand=true;
        return FILE_ERR_NONE;
      }else{
        // reseting to root dir
        configResetPlayingPath();
        //now prepare default playing file
        browser_build_list(true);
        memcpy(sort_list_play,sort_list,sizeof(sort_list));
        sdConfig.play_count_files=sort_list_len;
        sdConfig.play_cur_start=cursor_offset;
        sdConfig.play_cur=sdConfig.dir_cur;
        player_full_path(sdConfig.play_cur,lfn,sizeof(lfn));
        if(sd_play_file.open(lfn,O_RDONLY)){
          sd_play_file.close();
          PlayerCTRL.autoPlay=false;
          PlayerCTRL.isBrowserCommand=true;
          return FILE_ERR_NONE;
        }
      }
    }else{
      // reseting
      configResetPlayingPath();
      sort_list_len=0;
      sdConfig.play_count_files=sort_list_len;
      sdConfig.play_cur_start=0;
      sort_list_len=0;
      // now prepare default playing file
      browser_search_files_in_sd_dir(true);
      memcpy(sort_list_play,sort_list,sizeof(sort_list));
      sdConfig.play_count_files=sort_list_len;
      sdConfig.play_cur_start=cursor_offset;
      sdConfig.play_cur=sdConfig.dir_cur=cursor_offset;
      player_full_path(sdConfig.play_cur,lfn,sizeof(lfn));
      if(sd_play_file.open(lfn,O_RDONLY)){
        sd_play_file.close();
        PlayerCTRL.autoPlay=false;
        PlayerCTRL.isBrowserCommand=true;
        return FILE_ERR_NONE;
      }
    }
  }else{  // check if last played dir exists
    char buf[MAX_PATH];
    strncpy(buf,sdConfig.play_dir,sizeof(sdConfig.play_dir)-1);
    if(sd_play_dir.open(sdConfig.play_dir,O_RDONLY)){
      sd_play_dir.close();
      //now prepare playing file
      browser_build_list(true);
      memcpy(sort_list_play,sort_list,sizeof(sort_list));
      sdConfig.play_count_files=sort_list_len;
      sdConfig.play_cur_start=cursor_offset;
      sdConfig.dir_cur=sdConfig.play_cur;
      player_full_path(sdConfig.play_cur,lfn,sizeof(lfn));
      uint8_t file_type = browser_check_ext(lfn);
      if(sd_play_file.open(lfn,O_RDONLY)&&sd_play_file.isFile()&&file_type!=TYPE_UNK){
        sd_play_file.close();
        PlayerCTRL.autoPlay=false;
        PlayerCTRL.isBrowserCommand=true;
        return FILE_ERR_NONE;
      }else{
        // reseting
        configResetPlayingPath();
        sort_list_len=0;
        sdConfig.play_count_files=sort_list_len;
        sdConfig.play_cur_start=0;
        sort_list_len=0;
        // now prepare default playing file
        browser_search_files_in_sd_dir(true);
        memcpy(sort_list_play,sort_list,sizeof(sort_list));
        sdConfig.play_count_files=sort_list_len;
        sdConfig.play_cur_start=cursor_offset;
        sdConfig.play_cur=sdConfig.dir_cur=cursor_offset;
        player_full_path(sdConfig.play_cur,lfn,sizeof(lfn));
        if(sd_play_file.open(lfn,O_RDONLY)){
          sd_play_file.close();
          PlayerCTRL.autoPlay=false;
          PlayerCTRL.isBrowserCommand=true;
          return FILE_ERR_NONE;
        }
        return FILE_ERR_NONE;
      }
    }else{
      // reseting
      configResetPlayingPath();
      sort_list_len=0;
      sdConfig.play_count_files=sort_list_len;
      sdConfig.play_cur_start=0;
      sort_list_len=0;
      // now prepare default playing file
      browser_search_files_in_sd_dir(true);
      memcpy(sort_list_play,sort_list,sizeof(sort_list));
      sdConfig.play_count_files=sort_list_len;
      sdConfig.play_cur_start=cursor_offset;
      sdConfig.play_cur=sdConfig.dir_cur=cursor_offset;
      player_full_path(sdConfig.play_cur,lfn,sizeof(lfn));
      if(sd_play_file.open(lfn,O_RDONLY)){
        sd_play_file.close();
        PlayerCTRL.autoPlay=false;
        PlayerCTRL.isBrowserCommand=true;
        return FILE_ERR_NONE;
      }
      return FILE_ERR_NONE;
    }
  }
  return err;
}

void music_init(){
  muteAmp();
  AYInfo.module=music_data;
  AYInfo.module_len=music_data_size;
  AYInfo.file_data=music_data;
  AYInfo.file_len=music_data_size;
  switch(PlayerCTRL.music_type){
    case TYPE_PT1: PT1_Init(AYInfo); PT1_GetInfo(AYInfo); break;
    case TYPE_PT2: PT2_Init(AYInfo); PT2_GetInfo(AYInfo); break;
    case TYPE_PT3: PT3_Init(AYInfo); PT3_GetInfo(AYInfo); break;
    case TYPE_STC: STC_Init(AYInfo); STC_GetInfo(AYInfo); break;
    case TYPE_STP: STP_Init(AYInfo); STP_GetInfo(AYInfo); break;
    case TYPE_ASC: ASC_Init(AYInfo); ASC_GetInfo(AYInfo); break;
    case TYPE_PSC: PSC_Init(AYInfo); PSC_GetInfo(AYInfo); break;
    case TYPE_SQT: SQT_Init(AYInfo); SQT_GetInfo(AYInfo); break;
    case TYPE_AY: AY_Init(AYInfo); AY_GetInfo(AYInfo); break;
    case TYPE_PSG: break;
    case TYPE_RSF: break;
    case TYPE_YRG: break;
    case TYPE_MOD: break;
    case TYPE_S3M: break;
  #if defined(CONFIG_IDF_TARGET_ESP32S3)
    case TYPE_XM: break;
  #endif
    case TYPE_TAP: break;
    case TYPE_TZX: break;
    case TYPE_MP3: break;
    case TYPE_WAV: break;
  }
  unMuteAmp();
}

void music_play(){
#if defined(CONFIG_IDF_TARGET_ESP32S3)
  static uint8_t last_play_mode=255;
  static bool loop_change_pending=false;
#endif

  if(lfsConfig.play_mode==PLAY_MODE_ONE){
    if(PlayerCTRL.music_type!=TYPE_PSG
      &&PlayerCTRL.music_type!=TYPE_RSF
      &&PlayerCTRL.music_type!=TYPE_YRG
      &&PlayerCTRL.music_type!=TYPE_AY
      &&PlayerCTRL.music_type!=TYPE_MOD
      &&PlayerCTRL.music_type!=TYPE_S3M
      &&PlayerCTRL.music_type!=TYPE_TAP
      &&PlayerCTRL.music_type!=TYPE_TZX
      &&PlayerCTRL.music_type!=TYPE_MP3
      &&PlayerCTRL.music_type!=TYPE_WAV
    ){
    #if defined(CONFIG_IDF_TARGET_ESP32S3)
      if(PlayerCTRL.music_type==TYPE_XM){
        if(xm&&xm->isRunning()&&last_play_mode!=PLAY_MODE_ONE&&!loop_change_pending){
          xm->SetLoop(true);
          loop_change_pending=true;
        }
      }else
    #endif
      if(PlayerCTRL.trackFrame>=AYInfo.Length){
        if(AYInfo.Loop>0){
          PlayerCTRL.trackFrame=AYInfo.Loop;
        }else{
          PlayerCTRL.trackFrame-=AYInfo.Length; // =0
        }
      }
    }else{
      if(PlayerCTRL.trackFrame>=AYInfo.Length){
        PlayerCTRL.isFinish=true;
        return;
      }
    }
  }else{
  #if defined(CONFIG_IDF_TARGET_ESP32S3)
    if(PlayerCTRL.music_type==TYPE_XM){
      if(xm&&xm->isRunning()&&last_play_mode!=lfsConfig.play_mode&&!loop_change_pending){
        xm->SetLoop(false);
        loop_change_pending=true;
      }
    }
  #endif
    if(PlayerCTRL.trackFrame>=AYInfo.Length){
      if(PlayerCTRL.music_type!=TYPE_TAP&&PlayerCTRL.music_type!=TYPE_TZX){
        PlayerCTRL.isFinish=true;
        return;
      }
    }
  }
#if defined(CONFIG_IDF_TARGET_ESP32S3)
  if(last_play_mode!=lfsConfig.play_mode){
    last_play_mode=lfsConfig.play_mode;
    loop_change_pending=false; // Reset pending flag when mode actually changes
  }
#endif
  switch(PlayerCTRL.music_type){
    case TYPE_PT1: PT1_Play(AYInfo); break;
    case TYPE_PT2: PT2_Play(AYInfo); break;
    case TYPE_PT3: PT3_Play(AYInfo); break;
    case TYPE_STC: STC_Play(AYInfo); break;
    case TYPE_STP: STP_Play(AYInfo); break;
    case TYPE_ASC: ASC_Play(AYInfo); break;
    case TYPE_PSC: PSC_Play(AYInfo); break;
    case TYPE_SQT: SQT_Play(AYInfo); break;
    case TYPE_AY:  break; //AY files play differently, they're running Z80 emulation tied to the sound ISR
    case TYPE_PSG: PSG_Play(); break;
    case TYPE_RSF: RSF_Play(); break;
    case TYPE_YRG: YRG_Play(); break;
    case TYPE_MOD: MOD_Play(); break;
    case TYPE_S3M: S3M_Play(); break;
  #if defined(CONFIG_IDF_TARGET_ESP32S3)
    case TYPE_XM: XM_Play(); break;
  #endif
    case TYPE_TAP: TAP_Play(); break;
    case TYPE_TZX: TZX_Play(); break;
    case TYPE_MP3: MP3_Play(); break;
    case TYPE_WAV: WAV_Play(); break;
  }
}

void music_stop(){
  muteAmp();
  ay_reset();
  switch(PlayerCTRL.music_type){
    case TYPE_PT1: PT1_Cleanup(AYInfo); break;
    case TYPE_PT2: PT2_Cleanup(AYInfo); break;
    case TYPE_PT3: PT3_Cleanup(AYInfo); break;
    case TYPE_STC: STC_Cleanup(AYInfo); break;
    case TYPE_STP: STP_Cleanup(AYInfo); break;
    case TYPE_ASC: ASC_Cleanup(AYInfo); break;
    case TYPE_PSC: PSC_Cleanup(AYInfo); break;
    case TYPE_SQT: SQT_Cleanup(AYInfo); break;
    case TYPE_AY: AY_Cleanup(AYInfo); break;
    case TYPE_PSG: PSG_Cleanup(); break;
    case TYPE_RSF: RSF_Cleanup(); break;
    case TYPE_YRG: YRG_Cleanup(); break;
    case TYPE_MOD: MOD_Cleanup(); break;
    case TYPE_S3M: S3M_Cleanup(); break;
  #if defined(CONFIG_IDF_TARGET_ESP32S3)
    case TYPE_XM: XM_Cleanup(); break;
  #endif
    case TYPE_TAP: TAP_Cleanup(); break;
    case TYPE_TZX: TZX_Cleanup(); break;
    case TYPE_MP3: MP3_Cleanup(); break;
    case TYPE_WAV: WAV_Cleanup(); break;
  }
  PlayerCTRL.trackFrame=0;
#ifdef DEBUG_RAM
  printf("Music stop\n");
  checkHeap();
#endif
}

void check_cursor_range(){
  if(sdConfig.play_cur>sdConfig.play_count_files-1) sdConfig.play_cur=sdConfig.play_cur_start;
  if(sdConfig.play_cur<sdConfig.play_cur_start) sdConfig.play_cur=sdConfig.play_count_files-1;
  sd_config_save();
}

void changeTrackIcon(bool next=true){
  if(PlayerCTRL.screen_mode==SCR_PLAYER){
    img.setColorDepth(8);
    img.createSprite(13,13);
    img.fillScreen(0);
    if(next) img.drawBitmap(0,0,playerIcons13x13[NEXT],13,13,TFT_BLACK,TFT_YELLOW);
    else img.drawBitmap(0,0,playerIcons13x13[PREV],13,13,TFT_BLACK,TFT_YELLOW);
    img.pushSprite(114,173);
    img.deleteSprite();
  }
}

void playFinish(){ 
  muteAmp();
  //reset frames
  frame_cnt=0;
  PlayerCTRL.trackFrame=0;
  // reset all scroll
  memset(sPos,0,sizeof(sPos));
  memset(scrollDir,true,sizeof(scrollDir));
  memset(scrollbuf,0,sizeof(scrollbuf));
  memset(mlsS,0,sizeof(mlsS));
  // prepare finish
  PlayerCTRL.isPlay=false;
  music_stop();
  muteAYBeep();
  switch(lfsConfig.play_mode){
    case PLAY_MODE_ONE:
      if(PlayerCTRL.autoPlay){
        if(PlayerCTRL.music_type==TYPE_AY&&AY_GetNumSongs>0){
          ay_cur_song++;
          if(ay_cur_song>AY_GetNumSongs()){
            ay_cur_song=0;
            changeTrackIcon(true);
          }
        }else{
          changeTrackIcon(true);
        }
      }
      check_cursor_range();
      break;
    case PLAY_MODE_ALL:
      if(PlayerCTRL.autoPlay){
        if(PlayerCTRL.music_type==TYPE_AY&&AY_GetNumSongs>0){
          ay_cur_song++;
          if(ay_cur_song>AY_GetNumSongs()){
            ay_cur_song=0;
            changeTrackIcon(true);
            sdConfig.play_cur++;
          }
        }else{
          changeTrackIcon(true);
          sdConfig.play_cur++;
        }
      }
      check_cursor_range();
      if(lfsConfig.skipTapeFormats&&PlayerCTRL.autoPlay&&PlayerCTRL.music_type!=TYPE_AY){
        char tempPath[MAX_PATH];
        int attempts=0;
        while(attempts<sdConfig.play_count_files-sdConfig.play_cur_start){
          if(player_full_path(sdConfig.play_cur,tempPath,sizeof(tempPath))){
            int type=browser_check_ext(tempPath);
            if(type!=TYPE_TAP&&type!=TYPE_TZX) break;
          }
          sdConfig.play_cur++;
          check_cursor_range();
          attempts++;
        }
      }
      break;
    case PLAY_MODE_SHUFFLE:
      if(PlayerCTRL.autoPlay){
        if(PlayerCTRL.music_type==TYPE_AY&&AY_GetNumSongs>0){
          ay_cur_song++;
          if(ay_cur_song>AY_GetNumSongs()){
            ay_cur_song=0;
            changeTrackIcon(true);
            player_shuffle_cur();
          }
        }else{
          changeTrackIcon(true);
          player_shuffle_cur();
        }
      }
      check_cursor_range();
      if(lfsConfig.skipTapeFormats&&PlayerCTRL.autoPlay&&PlayerCTRL.music_type!=TYPE_AY){
        char tempPath[MAX_PATH];
        int attempts=0;
        while(attempts<sdConfig.play_count_files-sdConfig.play_cur_start){
          if(player_full_path(sdConfig.play_cur,tempPath,sizeof(tempPath))){
            int type=browser_check_ext(tempPath);
            if(type!=TYPE_TAP&&type!=TYPE_TZX) break;
          }
          player_shuffle_cur();
          attempts++;
        }
      }
      break;
  }
  sd_config_save();
  PlayerCTRL.autoPlay=true;
}

void player(){
  if(xSemaphoreTake(sdCardSemaphore,portMAX_DELAY)==pdTRUE){
    if(!sd_fat.card()->sectorCount()){
      xSemaphoreGive(sdCardSemaphore);  // Release the semaphore
      PlayerCTRL.isFinish=true;
      PlayerCTRL.scr_mode_update[SCR_PLAYER]=true;
      PlayerCTRL.isSDeject=true;
      PlayerCTRL.screen_mode=SCR_SDEJECT;
      return;
    }
    xSemaphoreGive(sdCardSemaphore);  // Release the semaphore
  }
  if(lfsConfig.playerSource==PLAYER_MODE_SD){
    if(PlayerCTRL.isFinish){
      // FIX: Removed duplicate xSemaphoreGive - semaphore already released at line 657
      playFinish();
      muteAYBeep();
      if(sdConfig.isPlayAYL){
        playlist_get_entry_full_path(sdConfig.play_cur,lfn,sizeof(lfn),true);
        if(sdConfig.play_prev_cur!=sdConfig.play_cur){
          ay_cur_song=0;
        }
        sdConfig.play_prev_cur=sdConfig.play_cur;
      }else{
        player_full_path(sdConfig.play_cur,lfn,sizeof(lfn));
        if(prev_file_id!=sort_list_play[sdConfig.play_cur].file_id){
          ay_cur_song=0;
        }
        prev_file_id=sort_list_play[sdConfig.play_cur].file_id;
      }
      memcpy(playFileName,lfn,sizeof(lfn));
      music_open(playFileName,ay_cur_song);
      music_init();
      PlayerCTRL.scr_mode_update[SCR_BROWSER]=true;
      browser_rebuild=1;
      PlayerCTRL.isFinish=false;
      if(PlayerCTRL.music_type==TYPE_TAP||PlayerCTRL.music_type==TYPE_TZX){
        if(PlayerCTRL.isBrowserCommand||lfsConfig.skipTapeFormats){
          PlayerCTRL.isPlay=false;
        }else{
          PlayerCTRL.isPlay=true;
        }
      }else{
        PlayerCTRL.isPlay=true;
      }
      PlayerCTRL.isBrowserCommand=false;
      return;
    }else{
      switch(PlayerCTRL.music_type){
      case TYPE_PSG:
      case TYPE_RSF:
      case TYPE_YRG:
        if(xSemaphoreTake(sdCardSemaphore,portMAX_DELAY)==pdTRUE){
          fillBuffer();
          xSemaphoreGive(sdCardSemaphore);  // Release the semaphore
        }
        break;
      default:
        break;
      }
    }
    if(!PlayerCTRL.isPlay){
      muteAYBeep();
    }
  }
}

void scrollInfos(char *txt, uint8_t textSize, uint16_t textColor, int width, int height, int xPos, int yPos, uint8_t scrollNumber=1){
  bool scroll=false;
  int strSize=tft_strlen(txt,textSize);
  if(strSize>width) scroll=true;
  if(scroll){
    if(millis()-mlsS[scrollNumber]>sUp[scrollNumber]){
      img.setColorDepth(8);
      img.createSprite(width,height);
      img.fillScreen(0);
      img.setFreeFont(&WildFont);
      img.setTextSize(textSize);
      img.setTextWrap(false);
      img.setTextColor(textColor);
      img.setCursor((sPos[scrollNumber]-(sPos[scrollNumber]*2)),16);
      img.print(utf8rus(txt));
      sUp[scrollNumber]=sUpC[scrollNumber];
      if(strSize-sPos[scrollNumber]>=width&&scrollDir[scrollNumber]){
        sPos[scrollNumber]++;
        if(strSize-sPos[scrollNumber]<width){scrollDir[scrollNumber]=false;sUp[scrollNumber]=S_UPD_DIR;}
      }
      if(!scrollDir[scrollNumber]){
        sPos[scrollNumber]--;
        if(sPos[scrollNumber]<0){scrollDir[scrollNumber]=true;sUp[scrollNumber]=S_UPD_DIR;}
      }
      mlsS[scrollNumber]=millis();
      img.pushSprite(xPos,yPos);
      img.deleteSprite();
    }
  } else {
    img.setColorDepth(8);
    img.createSprite(width,height);
    img.fillScreen(0);
    img.setFreeFont(&WildFont);
    img.setTextSize(textSize);
    img.setTextWrap(false);
    img.setTextColor(textColor);
    img.setCursor(0,textSize*8);
    img.print(utf8rus(txt));
    img.pushSprite(xPos,yPos);
    img.deleteSprite();
  }
}

void showFileInfo(){
  if(lfsConfig.playerSource==PLAYER_MODE_SD){
    //current Track / Tracks count
    img.setColorDepth(8);
    img.createSprite(12*7,8*2);
    img.setFreeFont(&WildFont);
    img.setTextSize(2);
    img.fillScreen(0);
    uint8_t shift=0;
    img.setCursor(8,16);
    img.setTextColor(WILD_CYAN,TFT_BLACK,true);
    sprintf(tme,"%03d",sdConfig.play_cur-sdConfig.play_cur_start+1);
    img.print(tme);
    img.print("/");
    sprintf(tme,"%03d",sdConfig.play_count_files-sdConfig.play_cur_start);
    img.print(tme);
    img.pushSprite(148,62);
    img.deleteSprite();
  }
  // file type
  if(lfsConfig.playerSource==PLAYER_MODE_SD){
    if(PlayerCTRL.music_type==TYPE_AY){
      if(AY_GetNumSongs()==0){
        sprintf(tme,"%S",file_ext_list[PlayerCTRL.music_type]);
      }else{
        sprintf(tme, "%S %u/%u",file_ext_list[PlayerCTRL.music_type],ay_cur_song+1,AY_GetNumSongs()+1);
      }
    }else if(PlayerCTRL.music_type==TYPE_TAP){
      if(tap_total_blocks==0){
        sprintf(tme,"%S",file_ext_list[PlayerCTRL.music_type]);
      }else{
        sprintf(tme,"%S %d/%d",file_ext_list[PlayerCTRL.music_type],(tap_cur_block+1>tap_total_blocks)?tap_total_blocks:tap_cur_block+1,tap_total_blocks);
      }
    }else if(PlayerCTRL.music_type==TYPE_TZX){
      if(tzx_total_blocks==0){
        sprintf(tme,"%S",file_ext_list[PlayerCTRL.music_type]);
      }else{
        sprintf(tme,"%S %d/%d",file_ext_list[PlayerCTRL.music_type],(tzx_cur_block+1>tzx_total_blocks)?tzx_total_blocks:tzx_cur_block+1,tzx_total_blocks);
      }
    }else if(PlayerCTRL.music_type==TYPE_MOD
      ||PlayerCTRL.music_type==TYPE_S3M
    #if defined(CONFIG_IDF_TARGET_ESP32S3)
      ||PlayerCTRL.music_type==TYPE_XM
    #endif
    ){
      sprintf(tme,"%s %s%u%s",file_ext_list[PlayerCTRL.music_type],(modChannels>9)?"":" ",modChannels,"Ch");
    }else if(PlayerCTRL.music_type==TYPE_MP3||PlayerCTRL.music_type==TYPE_WAV){
      if(PlayerCTRL.music_type==TYPE_MP3&&isVBR) sprintf(tme,"%s %u",file_ext_list[PlayerCTRL.music_type],bitrate);
      else sprintf(tme,"%s %uk/s",file_ext_list[PlayerCTRL.music_type],bitrate);
    }else{
      sprintf(tme,"%S",file_ext_list[PlayerCTRL.music_type]);
    }
  }else if(lfsConfig.playerSource==PLAYER_MODE_UART){
    sprintf(tme,"%S","UART");
  }
  img.setColorDepth(8);
  img.createSprite((23*10)-2,16);
  img.setTextSize(2);
  img.setCursor(0,16);
  img.setTextColor(WILD_CYAN);
  img.print("File type");
  img.setTextColor(TFT_RED);
  img.print(": ");
  img.setTextColor(TFT_YELLOW);
  img.print(tme);
  if(PlayerCTRL.music_type==TYPE_MP3&&isVBR){
    img.setTextColor(WILD_GREEN);
    img.print(" VBR");
    img.setTextColor(TFT_YELLOW);
  }
  img.pushSprite(9,220);
  img.deleteSprite();
  // is Turbo Sound
  if(AYInfo.is_ts&&lfsConfig.playerSource==PLAYER_MODE_SD){
    img.setColorDepth(8);
    img.createSprite((3*10)-2,16);
    img.fillScreen(0);
    img.setFreeFont(&WildFont);
    img.setTextSize(2);
    img.setTextColor((colCh2)?TFT_RED:TFT_WHITE);
    img.setCursor(0,16);
    img.print("TS!");
    img.pushSprite(180,220);
    img.deleteSprite();
    colCh2=!colCh2;
  }
  if(lfsConfig.playerSource==PLAYER_MODE_SD){
    // Name
    img.setColorDepth(8);
    img.createSprite((5*10)-2,16);
    img.fillScreen(0);
    img.setTextSize(2);
    img.setCursor(0,16);
    img.setTextColor(WILD_CYAN);
    img.print("Name");
    img.setTextColor(TFT_RED);
    img.print(":");
    img.pushSprite(9,238);
    img.deleteSprite();
    if(PlayerCTRL.music_type==TYPE_TZX){
      extern char tzxFullTitle[256];
      scrollInfos(tzxFullTitle,2,TFT_YELLOW,170,16,60,238,1);
    }else{
      scrollInfos(AYInfo.Name,2,TFT_YELLOW,170,16,60,238,1);
    }
    // Author / Block type
    if(PlayerCTRL.music_type==TYPE_TAP||PlayerCTRL.music_type==TYPE_TZX){
      // For tape formats: show block type as label, block name as text
      static char prevBlockTypeLabel[16]="";
      int labelLen = strlen(blockTypeLabel);
      int labelWidth = (labelLen*10)+10;
      int scrollXPos = 9 + labelWidth;
      int scrollWidth = 230 - scrollXPos;
      if(strcmp(prevBlockTypeLabel,blockTypeLabel)!=0){
        tft.fillRect(9,256,221,16,TFT_BLACK);
        strcpy(prevBlockTypeLabel,blockTypeLabel);
      }
      img.setColorDepth(8);
      img.createSprite(labelWidth,16);
      img.fillScreen(0);
      img.setTextSize(2);
      img.setCursor(0,16);
      img.setTextColor(WILD_CYAN);
      img.print(blockTypeLabel);
      img.setTextColor(TFT_RED);
      img.print(":");
      img.pushSprite(9,256);
      img.deleteSprite();
      scrollInfos(AYInfo.Author,2,TFT_YELLOW,scrollWidth,16,scrollXPos,256,2);
    }else{
      // For other formats: show "Author" as label
      img.setColorDepth(8);
      img.createSprite((6*10)+10,16);
      img.fillScreen(0);
      img.setTextSize(2);
      img.setCursor(0,16);
      img.setTextColor(WILD_CYAN);
      img.print("Author");
      img.setTextColor(TFT_RED);
      img.print(":");
      img.pushSprite(9,256);
      img.deleteSprite();
      scrollInfos(AYInfo.Author,2,TFT_YELLOW,150,16,80,256,2);
    }
    // File name
    img.setColorDepth(8);
    img.createSprite((5*10)-2,16);
    img.fillScreen(0);
    img.setTextSize(2);
    img.setCursor(0,16);
    img.setTextColor(WILD_CYAN);
    img.print("File");
    img.setTextColor(TFT_RED);
    img.print(":");
    img.pushSprite(9,274);
    img.deleteSprite();
    scrollInfos(playedFileName,2,TFT_YELLOW,170,16,60,274,3);
  }
}

void playerFrameShow(){
  //show logo
  tft.pushImage(8,8,186,44,wildLogo186x44);
  uint8_t shift=10;
  if(lfsConfig.playerSource==PLAYER_MODE_SD){
    for(uint8_t i=0;i<36;i++){
      tft.fillRect(shift,70,2,2,TFT_BLUE);
      shift+=4;
    }
  }else if(lfsConfig.playerSource==PLAYER_MODE_UART){
    for(uint8_t i=0;i<56;i++){
      tft.fillRect(shift,70,2,2,TFT_BLUE);
      shift+=4;
    }
  }
  // blue delemiter under time
  img.setColorDepth(8);
  img.createSprite(224,2);
  img.fillScreen(0);
  shift=0;
  for(uint8_t i=0;i<56;i++){
    img.fillRect(shift,0,2,2,TFT_BLUE);
    shift+=4;
  }
  img.pushSprite(9,194);
  img.deleteSprite();
  voltage();
}

void timeShow(){
  //file play position
  img.setColorDepth(8);
  img.createSprite(222,4);
  img.fillScreen(0);
  uint8_t step=0;
  for(uint8_t i=0;i<111;i++){
    if(i%2==0){
      img.fillRect(step,0,2,2,WILD_YELLOW);
      step+=2;
    }else{
      img.fillRect(step,2,2,2,WILD_YELLOW);
      step+=2;
    }
  }
  static unsigned long tF=0;
  if(PlayerCTRL.trackFrame>=AYInfo.Length) tF=AYInfo.Length;
  else tF=PlayerCTRL.trackFrame;
  img.fillRect(0,0,map(tF,0,AYInfo.Length,1,222),4,TFT_YELLOW);
  img.pushSprite(9,161);
  img.deleteSprite();
  //time elapsed
  sprintf(tme, "%2.2u:%2.2u:%2.2u", PlayerCTRL.trackFrame/50/60, PlayerCTRL.trackFrame/50%60, PlayerCTRL.trackFrame*2%100);
  img.setColorDepth(8);
  img.createSprite((8*10)-2,8);
  img.setFreeFont(&WildFont);
  img.setTextSize(2);
  img.fillScreen(0);
  img.setCursor(0,16);
  img.setTextColor(TFT_WHITE,TFT_BLACK,true);
  img.print(tme);
  img.pushSprite(9,172);
  img.deleteSprite();
  img.setColorDepth(8);
  img.createSprite((8*10)-2,8);
  img.setFreeFont(&WildFont);
  img.setTextSize(2);
  img.fillScreen(0);
  img.setCursor(0,8);
  img.setTextColor(WILD_CYAN_D2,TFT_BLACK,true);
  img.print(tme);
  img.pushSprite(9,172+8);
  img.deleteSprite();
  //track time
  if(PlayerCTRL.music_type==TYPE_TAP||PlayerCTRL.music_type==TYPE_TZX){
    sprintf(tme, "~%2.2u:%2.2u:%2.2u", AYInfo.Length/50/60, AYInfo.Length/50%60, AYInfo.Length*2%100);
    img.setColorDepth(8);
    img.createSprite((9*10)-2,8);
    img.setFreeFont(&WildFont);
    img.setTextSize(2);
    img.fillScreen(0);
    img.setCursor(0,16);
    img.setTextColor(TFT_WHITE,TFT_BLACK,true);
    img.print(tme);
    img.pushSprite(153-10,172);
    img.deleteSprite();
    img.setColorDepth(8);
    img.createSprite((9*10)-2,8);
    img.setFreeFont(&WildFont);
    img.setTextSize(2);
    img.fillScreen(0);
    img.setCursor(0,8);
    img.setTextColor(WILD_CYAN_D2,TFT_BLACK,true);
    img.print(tme);
    img.pushSprite(153-10,172+8);
    img.deleteSprite();
  }else{
    sprintf(tme, "%2.2u:%2.2u:%2.2u", AYInfo.Length/50/60, AYInfo.Length/50%60, AYInfo.Length*2%100);
    img.setColorDepth(8);
    img.createSprite((8*10)-2,8);
    img.setFreeFont(&WildFont);
    img.setTextSize(2);
    img.fillScreen(0);
    img.setCursor(0,16);
    img.setTextColor(TFT_WHITE,TFT_BLACK,true);
    img.print(tme);
    img.pushSprite(153,172);
    img.deleteSprite();
    img.setColorDepth(8);
    img.createSprite((8*10)-2,8);
    img.setFreeFont(&WildFont);
    img.setTextSize(2);
    img.fillScreen(0);
    img.setCursor(0,8);
    img.setTextColor(WILD_CYAN_D2,TFT_BLACK,true);
    img.print(tme);
    img.pushSprite(153,172+8);
    img.deleteSprite();
  }
}

void uartInfoShow(){
  // UART mode label
  sprintf(tme, "%S", "UART MODE");
  img.setColorDepth(8);
  img.createSprite((9*15)-2,12);
  img.setFreeFont(&WildFont);
  img.setTextSize(3);
  img.fillScreen(0);
  img.setCursor(0,24);
  img.setTextColor(TFT_WHITE,TFT_BLACK,true);
  img.print(tme);
  img.pushSprite(54,162);
  img.deleteSprite();
  img.setColorDepth(8);
  img.createSprite((9*15)-2,12);
  img.setFreeFont(&WildFont);
  img.setTextSize(3);
  img.fillScreen(0);
  img.setCursor(0,12);
  img.setTextColor(WILD_CYAN_D2,TFT_BLACK,true);
  img.print(tme);
  img.pushSprite(54,162+12);
  img.deleteSprite();
  // print bottom info about UART mode (zero point sprite: 9,238(242?)) max width:222, max height: 52(48?)
  img.setColorDepth(8);
  img.createSprite((21*10)-2,16);
  img.setFreeFont(&WildFont);
  img.setTextSize(2);
  img.fillScreen(0);
  img.setTextColor(WILD_RED,TFT_BLACK,true);
  img.setCursor(10,16);
  img.print("Connect ZxPOD to PC");
  img.pushSprite(16,246);
  img.deleteSprite();

  img.setColorDepth(8);
  img.createSprite((14*10)-2,16);
  img.setFreeFont(&WildFont);
  img.setTextSize(2);
  img.fillScreen(0);
  img.setTextColor(WILD_RED,TFT_BLACK,true);
  img.setCursor(0,16);
  img.print("at ");
  img.setTextColor(WILD_CYAN,TFT_BLACK,true);
  img.print("57600");
  img.setTextColor(WILD_RED,TFT_BLACK,true);
  img.print(" baud.");
  img.pushSprite(51,246+20);
  img.deleteSprite();
}

void ayClockShow(){
  // ay clock show
  if(PlayerCTRL.music_type==TYPE_MOD
    ||PlayerCTRL.music_type==TYPE_S3M
  #if defined(CONFIG_IDF_TARGET_ESP32S3)
    ||PlayerCTRL.music_type==TYPE_XM
  #endif
  ){
    switch(lfsConfig.modStereoSeparation){
      case MOD_FULLSTEREO: sprintf(tme,"Full Stereo");break;
      case MOD_HALFSTEREO: sprintf(tme,"Half Stereo");break;
      case MOD_MONO: sprintf(tme,"Mono");break;
    }
  }else if(PlayerCTRL.music_type==TYPE_TAP||PlayerCTRL.music_type==TYPE_TZX){
    switch(lfsConfig.tapeSpeed){
      case TAPE_NORMAL: sprintf(tme,"Normal 3.5MHz");break;
      case TAPE_TURBO1: sprintf(tme,"Turbo 7MHz");break;
      case TAPE_TURBO2: sprintf(tme,"Turbo 14MHz");break;
    }
  }else if(PlayerCTRL.music_type==TYPE_MP3||PlayerCTRL.music_type==TYPE_WAV){
    switch(channelMode){
      case 0: sprintf(tme,"Stereo");break;
      case 1: sprintf(tme,"Joint Stereo");break;
      case 2: sprintf(tme,"Dual Channel");break;
      case 3: sprintf(tme,"Mono");break;
    }
  }else{
    switch(lfsConfig.ay_clock){
      case CLK_SPECTRUM: sprintf(tme,"ZX 1.77MHz");break;
      case CLK_PENTAGON: sprintf(tme,"PEN 1.75MHz");break;
      case CLK_MSX: sprintf(tme,"MSX 1.78MHz");break;
      case CLK_CPC: sprintf(tme,"CPC 1.0MHz");break;
      case CLK_ATARIST: sprintf(tme,"ST 2.0MHz");break;
    }
  }
  img.setColorDepth(8);
  img.createSprite((22*10)-2,16);
  img.setTextSize(2);
  img.setCursor(0,16);
  img.setTextColor(WILD_CYAN);
  if(PlayerCTRL.music_type==TYPE_MOD
    ||PlayerCTRL.music_type==TYPE_S3M
  #if defined(CONFIG_IDF_TARGET_ESP32S3)
    ||PlayerCTRL.music_type==TYPE_XM
  #endif
  ) img.print("Stereo ");
  else if(PlayerCTRL.music_type==TYPE_TAP||PlayerCTRL.music_type==TYPE_TZX) img.print("Tape mode");
  else if(PlayerCTRL.music_type==TYPE_MP3||PlayerCTRL.music_type==TYPE_WAV) img.print("Mode");
  else img.print("AY clock");
  img.setTextColor(TFT_RED);
  img.print(": ");
  img.setTextColor(TFT_YELLOW);
  img.print(tme);
  img.pushSprite(9,202);
  img.deleteSprite();
}

void showPlayerIcons(){
  //play
  if(PlayerCTRL.isPlay&&!PlayerCTRL.isFastForward&&!PlayerCTRL.isSlowBackward){
    img.setColorDepth(8);
    img.createSprite(13,13);
    img.fillScreen(0);
    img.drawBitmap(0,0,playerIcons13x13[PLAY],13,13,TFT_BLACK,TFT_YELLOW);
    img.pushSprite(114,173);
    img.deleteSprite();
  }
  //pause
  if(!PlayerCTRL.isPlay){
    static bool pse=true;
    if(millis()-mls>500){
      img.setColorDepth(8);
      img.createSprite(13,13);
      img.fillScreen(0);
      if(pse) img.drawBitmap(0,0,playerIcons13x13[PAUSE],13,13,TFT_BLACK,TFT_YELLOW);
      img.pushSprite(114,173);
      img.deleteSprite();
      pse=!pse;
      mls=millis();
    }
  }
  //FWD
  if(PlayerCTRL.isFastForward&&PlayerCTRL.isPlay){
    static bool pse=true;
    if(millis()-mls>500){
      img.setColorDepth(8);
      img.createSprite(13,13);
      img.fillScreen(0);
      if(pse) img.drawBitmap(0,0,playerIcons13x13[FWD],13,13,TFT_BLACK,TFT_YELLOW);
      img.pushSprite(114,173);
      img.deleteSprite();
      pse=!pse;
      mls=millis();
    }
  }
  //BWD
  if(PlayerCTRL.isSlowBackward&&PlayerCTRL.isPlay){
    static bool pse=true;
    if(millis()-mls>500){
      img.setColorDepth(8);
      img.createSprite(13,13);
      img.setPivot(114+12,173+12);
      if(pse) img.drawBitmap(0,0,playerIcons13x13[FWD],13,13,TFT_BLACK,TFT_YELLOW);
      img.pushRotated(180);
      img.deleteSprite();
      pse=!pse;
      mls=millis();
    }
  }
}

void vbUpdate(){
  tft.fillRect(12,62,10*13,8*2,0);
  uint8_t shift=10;
  for(uint8_t i=0;i<36;i++){
    tft.fillRect(shift,70,2,2,TFT_BLUE);
    shift+=4;
  }
}

void showClock(){
  static bool flashState=true;
  static uint32_t lastFlashTime=0;
  // Check if it's time to toggle the flash state (every 500ms)
  if(millis()-lastFlashTime>500){
    flashState=!flashState;
    lastFlashTime=millis();
  }
  sprintf(tme,"%02d%s%02d",now.hour(),(flashState)?":":" ",now.minute());
  img.setColorDepth(8);
  img.createSprite(10*5,8*2);
  img.fillScreen(0);
  img.setFreeFont(&WildFont);
  img.setTextColor(TFT_MAGENTA);
  img.setTextSize(2);
  img.setCursor(2,16);
  img.print(tme);
  img.pushSprite(11,10);
  img.deleteSprite();
  sprintf(tme,"%s %02d %s %04d",daysOfTheWeekShort[now.dayOfTheWeek()],now.day(),monthsOfTheYear[now.month()],now.year());
  if(clockShowFlag) scrollInfos(tme,2,TFT_MAGENTA,10*13,8*2,10,62,4);
}

void player_screen(){
  if(PlayerCTRL.scr_mode_update[SCR_PLAYER]){
    clear_display_field();
    dynRebuild=true;
    playerFrameShow();
  }
  if(dynRebuild){
    // show play mode
    if(lfsConfig.playerSource==PLAYER_MODE_SD){
      tft.drawBitmap(199,22,spModes[lfsConfig.play_mode],30,30,TFT_BLACK,WILD_CYAN);
    }else if(lfsConfig.playerSource==PLAYER_MODE_UART){
      uartInfoShow();
    }
    if(!lfsConfig.showClock) vbUpdate();
  }
  dynRebuild=false;
  PlayerCTRL.scr_mode_update[SCR_PLAYER]=false;
  voltage();
  ayClockShow();
  showFileInfo();
  if(lfsConfig.playerSource==PLAYER_MODE_SD){
    if(PlayerCTRL.screen_mode!=SCR_ALERT){
      timeShow();
      showPlayerIcons();
    }
  }
  if(PlayerCTRL.screen_mode!=SCR_ALERT){
    fastEQ();
  }
  if(lfsConfig.showClock&&foundRtc) showClock();
  //keypad survey
  if(lfsConfig.playerSource==PLAYER_MODE_SD){
    if(enc.hasClicks(1)&&lcdBlackout==false&&scrNotPlayer==false){
      PlayerCTRL.isPlay=!PlayerCTRL.isPlay;
      PlayerCTRL.isPlay?unMuteAmp():muteAmp();
    }
    if(!enc.holding()&&enc.right()&&lcdBlackout==false&&scrNotPlayer==false){
      changeTrackIcon(true);
      if(lfsConfig.play_mode==PLAY_MODE_SHUFFLE) player_shuffle_cur();
      else sdConfig.play_cur++;
      PlayerCTRL.isBrowserCommand=true;
      PlayerCTRL.autoPlay=false;
      PlayerCTRL.isFinish=true;
      vTaskDelay(pdMS_TO_TICKS(30));  // Non-blocking delay
    }
    if(!enc.holding()&&enc.left()&&lcdBlackout==false&&scrNotPlayer==false){
      changeTrackIcon(false);
      if(millis()-mlsPrevTrack<PREVTRACKDELAY) sdConfig.play_cur--;
      mlsPrevTrack=millis()+loadingTime;
      loadingTime=0;
      PlayerCTRL.isBrowserCommand=true;
      PlayerCTRL.autoPlay=false;
      PlayerCTRL.isFinish=true;
      vTaskDelay(pdMS_TO_TICKS(30));  // Non-blocking delay
    }
    if(enc.rightH()&&lcdBlackout==false&&scrNotPlayer==false){
      if(PlayerCTRL.music_type!=TYPE_AY&&PlayerCTRL.music_type!=TYPE_TAP&&PlayerCTRL.music_type!=TYPE_TZX){
        if(PlayerCTRL.music_type==TYPE_MOD){
          if(mod&&mod->isRunning()) mod->setSpeed(2);
        }
        if(PlayerCTRL.music_type==TYPE_S3M){
          if(s3m&&s3m->isRunning()) s3m->setSpeed(2);
        }
      #if defined(CONFIG_IDF_TARGET_ESP32S3)
        if(PlayerCTRL.music_type==TYPE_XM){
          if(xm&&xm->isRunning()) xm->setSpeed(2);
        }
      #endif
        if(PlayerCTRL.music_type==TYPE_MP3){
          if(mp3&&mp3->isRunning()) mp3->setSpeed(2);
        }
        if(PlayerCTRL.music_type==TYPE_WAV){
          if(wav&&wav->isRunning()) wav->setSpeed(2);
        }
        frame_max=frameMax(PLAY_FAST);
        PlayerCTRL.isSlowBackward=false;
        PlayerCTRL.isFastForward=true;
      }else if(PlayerCTRL.music_type==TYPE_AY){
        ay_cur_song++;
        if(ay_cur_song>AY_GetNumSongs()) ay_cur_song=0;
        changeTrackIcon(true);
        PlayerCTRL.isFinish=true;
        PlayerCTRL.autoPlay=false;
        PlayerCTRL.isBrowserCommand=true;
      }else if(PlayerCTRL.music_type==TYPE_TAP){
        if(tap&&tap_cur_block<tap_total_blocks-1){
          tap_cur_block++;
          tap->setCurrentBlock(tap_cur_block);
          strcpy(blockTypeLabel, tap->getBlockType(tap_cur_block));
          tap->getBlockName(tap_cur_block, AYInfo.Author, sizeof(AYInfo.Author));
          PlayerCTRL.isPlay=false;
          muteAmp();
        }
      }else if(PlayerCTRL.music_type==TYPE_TZX){
        if(tzx&&tzx_cur_block<tzx_total_blocks-1){
          tzx_cur_block++;
          tzx->setCurrentBlock(tzx_cur_block);
          const char* blockType = tzx->getBlockType(tzx_cur_block);
          char blockName[32];
          memset(blockName, 0, sizeof(blockName));
          tzx->getBlockName(tzx_cur_block, blockName, sizeof(blockName));
          if(strlen(blockName)==0) snprintf(AYInfo.Author, sizeof(AYInfo.Author), "Block %d", tzx_cur_block+1);
          else snprintf(AYInfo.Author, sizeof(AYInfo.Author), "%s", blockName);
          snprintf(blockTypeLabel, sizeof(blockTypeLabel), "%s", blockType);
          PlayerCTRL.isPlay=false;
          muteAmp();
        }
      }
    }
    if(enc.leftH()&&lcdBlackout==false&&scrNotPlayer==false){
      if(PlayerCTRL.music_type!=TYPE_AY&&PlayerCTRL.music_type!=TYPE_TAP&&PlayerCTRL.music_type!=TYPE_TZX){
        if(PlayerCTRL.music_type==TYPE_MOD){
          if(mod&&mod->isRunning()) mod->setSpeed(0);
        }
        if(PlayerCTRL.music_type==TYPE_S3M){
          if(s3m&&s3m->isRunning()) s3m->setSpeed(0);
        }
      #if defined(CONFIG_IDF_TARGET_ESP32S3)
        if(PlayerCTRL.music_type==TYPE_XM){
          if(xm&&xm->isRunning()) xm->setSpeed(0);
        }
      #endif
        if(PlayerCTRL.music_type==TYPE_MP3){
          if(mp3&&mp3->isRunning()) mp3->setSpeed(0);
        }
        if(PlayerCTRL.music_type==TYPE_WAV){
          if(wav&&wav->isRunning()) wav->setSpeed(0);
        }
        frame_max=frameMax(PLAY_SLOW);
        PlayerCTRL.isFastForward=false;
        PlayerCTRL.isSlowBackward=true;
      }else if(PlayerCTRL.music_type==TYPE_AY){
        ay_cur_song--;
        if(ay_cur_song<0) ay_cur_song=AY_GetNumSongs();
        changeTrackIcon(false);
        PlayerCTRL.isFinish=true;
        PlayerCTRL.autoPlay=false;
        PlayerCTRL.isBrowserCommand=true;
      }else if(PlayerCTRL.music_type==TYPE_TAP){
        if(tap&&tap_cur_block>0){
          tap_cur_block--;
          tap->setCurrentBlock(tap_cur_block);
          strcpy(blockTypeLabel, tap->getBlockType(tap_cur_block));
          tap->getBlockName(tap_cur_block, AYInfo.Author, sizeof(AYInfo.Author));
          PlayerCTRL.isPlay=false;
          muteAmp();
        }
      }else if(PlayerCTRL.music_type==TYPE_TZX){
        if(tzx&&tzx_cur_block>0){
          tzx_cur_block--;
          tzx->setCurrentBlock(tzx_cur_block);
          const char* blockType = tzx->getBlockType(tzx_cur_block);
          char blockName[32];
          memset(blockName, 0, sizeof(blockName));
          tzx->getBlockName(tzx_cur_block, blockName, sizeof(blockName));
          if(strlen(blockName)==0) snprintf(AYInfo.Author, sizeof(AYInfo.Author), "Block %d", tzx_cur_block+1);
          else snprintf(AYInfo.Author, sizeof(AYInfo.Author), "%s", blockName);
          snprintf(blockTypeLabel, sizeof(blockTypeLabel), "%s", blockType);
          PlayerCTRL.isPlay=false;
          muteAmp();
        }
      }
    }
    if(enc.release()){
      if(PlayerCTRL.music_type==TYPE_MOD){
        if(mod&&mod->isRunning()) mod->setSpeed(1);
      }
      if(PlayerCTRL.music_type==TYPE_S3M){
        if(s3m&&s3m->isRunning()) s3m->setSpeed(1);
      }
    #if defined(CONFIG_IDF_TARGET_ESP32S3)
      if(PlayerCTRL.music_type==TYPE_XM){
        if(xm&&xm->isRunning()) xm->setSpeed(1);
      }
    #endif
      if(PlayerCTRL.music_type==TYPE_MP3){
        if(mp3&&mp3->isRunning()) mp3->setSpeed(1);
      }
      if(PlayerCTRL.music_type==TYPE_WAV){
        if(wav&&wav->isRunning()) wav->setSpeed(1);
      }
      frame_max=frameMax(PLAY_NORMAL);
      PlayerCTRL.isFastForward=false;
      PlayerCTRL.isSlowBackward=false;
    }
  }
  if((up.hasClicks(1)||up.holding())&&lcdBlackout==false&&scrNotPlayer==false){
    if(!enc.holding()){
      clockShowFlag=false;
      if(sdConfig.volume++>=63) sdConfig.volume=63;
      writeToAmp(AMP_REG2,(muteL<<7|muteR<<6|sdConfig.volume));
      img.setColorDepth(8);
      img.createSprite(10*13,8*2);
      img.fillScreen(0);
      img.setFreeFont(&WildFont);
      img.setTextColor(TFT_MAGENTA);
      img.setTextSize(2);
      img.setCursor(0,16);
      img.print("Volume:  ");
      img.setTextColor(WILD_YELLOW);
      if(sdConfig.volume>=63) img.print("max");
      else if(sdConfig.volume<=0) img.print("min");
      else img.print(sdConfig.volume);
      img.pushSprite(12,62);
      img.deleteSprite();
      sdFlag=true;
    }
  }
  if(lfsConfig.playerSource==PLAYER_MODE_SD){
    if(up.hasClicks(2)&&lcdBlackout==false&&scrNotPlayer==false){
      switch(lfsConfig.play_mode){
        case PLAY_MODE_ONE: lfsConfig.play_mode=PLAY_MODE_ALL;break;
        case PLAY_MODE_ALL: lfsConfig.play_mode=PLAY_MODE_SHUFFLE;break;
        case PLAY_MODE_SHUFFLE: lfsConfig.play_mode=PLAY_MODE_ONE;break;
      }
      dynRebuild=true;
      sdFlag=false;
    }
  }
  if((dn.hasClicks(1)||dn.holding())&&lcdBlackout==false&&scrNotPlayer==false){
    if(!enc.holding()){
      clockShowFlag=false;
      if(sdConfig.volume--<=0) sdConfig.volume=0;
      writeToAmp(AMP_REG2,(muteL<<7|muteR<<6|sdConfig.volume));
      img.setColorDepth(8);
      img.createSprite(10*13,8*2);
      img.fillScreen(0);
      img.setFreeFont(&WildFont);
      img.setTextColor(TFT_MAGENTA);
      img.setTextSize(2);
      img.setCursor(0,16);
      img.print("Volume:  ");
      img.setTextColor(WILD_YELLOW);
      if(sdConfig.volume>=63) img.print("max");
      else if(sdConfig.volume<=0) img.print("min");
      else img.print(sdConfig.volume);
      img.pushSprite(12,62);
      img.deleteSprite();
      sdFlag=true;
    }
  }
  if(dn.hasClicks(2)&&lcdBlackout==false&&scrNotPlayer==false){
    if(PlayerCTRL.music_type==TYPE_MOD
      ||PlayerCTRL.music_type==TYPE_S3M
    #if defined(CONFIG_IDF_TARGET_ESP32S3)
      ||PlayerCTRL.music_type==TYPE_XM
    #endif
    ){
      switch(lfsConfig.modStereoSeparation){
        case MOD_FULLSTEREO: lfsConfig.modStereoSeparation=MOD_HALFSTEREO;break;
        case MOD_HALFSTEREO: lfsConfig.modStereoSeparation=MOD_MONO;break;
        case MOD_MONO: lfsConfig.modStereoSeparation=MOD_FULLSTEREO;break;
      }
      if(PlayerCTRL.music_type==TYPE_MOD) setModSeparation();
      if(PlayerCTRL.music_type==TYPE_S3M) setS3mSeparation();
    #if defined(CONFIG_IDF_TARGET_ESP32S3)
      if(PlayerCTRL.music_type==TYPE_XM) setXmSeparation();
    #endif
    }else if(PlayerCTRL.music_type==TYPE_TAP||PlayerCTRL.music_type==TYPE_TZX){
      switch(lfsConfig.tapeSpeed){
        case TAPE_NORMAL: lfsConfig.tapeSpeed=TAPE_TURBO1;break;
        case TAPE_TURBO1: lfsConfig.tapeSpeed=TAPE_TURBO2;break;
        case TAPE_TURBO2: lfsConfig.tapeSpeed=TAPE_NORMAL;break;
      }
      if(PlayerCTRL.music_type==TYPE_TAP) setTapSpeed();
      if(PlayerCTRL.music_type==TYPE_TZX) setTzxSpeed();
    }else if(PlayerCTRL.music_type!=TYPE_MP3&&PlayerCTRL.music_type!=TYPE_WAV){
      switch(lfsConfig.ay_clock){
        case CLK_SPECTRUM: lfsConfig.ay_clock=CLK_PENTAGON;break;
        case CLK_PENTAGON: lfsConfig.ay_clock=CLK_MSX;break;
        case CLK_MSX: lfsConfig.ay_clock=CLK_CPC;break;
        case CLK_CPC: lfsConfig.ay_clock=CLK_ATARIST;break;
        case CLK_ATARIST: lfsConfig.ay_clock=CLK_SPECTRUM;break;
      }
      ay_set_clock(lfsConfig.ay_clock);
    }
    dynRebuild=true;
    sdFlag=false;
  }
  if((dn.timeout(2000)||up.timeout(2000))&&lcdBlackout==false){
    dynRebuild=true;
    sd_config_save();
    if(!sdFlag) lfs_config_save(); // Saving without volume
    sdFlag=false;
    clockShowFlag=true;
  }
  keysTimeOut();
}

void wait_frame(){
  uint32_t prev=frame_cnt;
  while(frame_cnt==prev&&PlayerCTRL.isPlay){
    yield();
    vTaskDelay(1);
    esp_task_wdt_reset();
  }
}

void AYPlayTask(void *pvParameters){
  while(true){
    if(PlayerCTRL.isSDeject){
      muteAYBeep();
      vTaskDelay(/*pdMS_TO_TICKS(1)*/1);
      esp_task_wdt_reset();
    }else{
      if(PlayerCTRL.isPlay&&!PlayerCTRL.isFinish){
        music_play();
      }
      if(PlayerCTRL.music_type==TYPE_AY){
        if(PlayerCTRL.isPlay&&!PlayerCTRL.isFinish){
          while(!Sound.buf_do_update){
            yield();
            vTaskDelay(1);
            esp_task_wdt_reset();
          }
          Sound.buf_do_update=false;
          AY_PlayBuf();
        }
      }else{
        if(PlayerCTRL.music_type!=TYPE_MOD
          &&PlayerCTRL.music_type!=TYPE_S3M
        #if defined(CONFIG_IDF_TARGET_ESP32S3)
          &&PlayerCTRL.music_type!=TYPE_XM
        #endif
          &&PlayerCTRL.music_type!=TYPE_TAP
          &&PlayerCTRL.music_type!=TYPE_TZX
          &&PlayerCTRL.music_type!=TYPE_MP3
          &&PlayerCTRL.music_type!=TYPE_WAV
        ) wait_frame();
      }
    }
    yield();
    vTaskDelay(1);
    esp_task_wdt_reset();
  }
  vTaskDelete(NULL);
}

void AYPlayCoreInit(){
  xTaskCreatePinnedToCore(
    AYPlayTask,  // Function to implement the task
    "AYPlay",    // Name of the task
    8192,       // Stack size in words
    NULL,        // Task input parameter
    2,           // Priority of the task
    &ayPlayTaskHandle,     // Task handle.
    0            // Core where the task should run
  );
}
