djspawnbrest/ESP32AY/src/players/z80/spectrum_rom.h

static const unsigned char spectrum_rom[] PROGMEM ={
0xf3,0xaf,0x11,0xff,0xff,0xc3,0xcb,0x11,0x2a,0x5d,0x5c,0x22,0x5f,0x5c,0x18,0x43,
0xc3,0xf2,0x15,0xff,0xff,0xff,0xff,0xff,0x2a,0x5d,0x5c,0x7e,0xcd,0x7d,0x00,0xd0,
0xcd,0x74,0x00,0x18,0xf7,0xff,0xff,0xff,0xc3,0x5b,0x33,0xff,0xff,0xff,0xff,0xff,
0xc5,0x2a,0x61,0x5c,0xe5,0xc3,0x9e,0x16,0xf5,0xe5,0x2a,0x78,0x5c,0x23,0x22,0x78,
0x5c,0x7c,0xb5,0x20,0x03,0xfd,0x34,0x40,0xc5,0xd5,0xcd,0xbf,0x02,0xd1,0xc1,0xe1,
0xf1,0xfb,0xc9,0xe1,0x6e,0xfd,0x75,0x00,0xed,0x7b,0x3d,0x5c,0xc3,0xc5,0x16,0xff,
0xff,0xff,0xff,0xff,0xff,0xff,0xf5,0xe5,0x2a,0xb0,0x5c,0x7c,0xb5,0x28,0x01,0xe9,
0xe1,0xf1,0xed,0x45,0x2a,0x5d,0x5c,0x23,0x22,0x5d,0x5c,0x7e,0xc9,0xfe,0x21,0xd0,
0xfe,0x0d,0xc8,0xfe,0x10,0xd8,0xfe,0x18,0x3f,0xd8,0x23,0xfe,0x16,0x38,0x01,0x23,
0x37,0x22,0x5d,0x5c,0xc9,0xbf,0x52,0x4e,0xc4,0x49,0x4e,0x4b,0x45,0x59,0xa4,0x50,
0xc9,0x46,0xce,0x50,0x4f,0x49,0x4e,0xd4,0x53,0x43,0x52,0x45,0x45,0x4e,0xa4,0x41,
0x54,0x54,0xd2,0x41,0xd4,0x54,0x41,0xc2,0x56,0x41,0x4c,0xa4,0x43,0x4f,0x44,0xc5,
0x56,0x41,0xcc,0x4c,0x45,0xce,0x53,0x49,0xce,0x43,0x4f,0xd3,0x54,0x41,0xce,0x41,
0x53,0xce,0x41,0x43,0xd3,0x41,0x54,0xce,0x4c,0xce,0x45,0x58,0xd0,0x49,0x4e,0xd4,
0x53,0x51,0xd2,0x53,0x47,0xce,0x41,0x42,0xd3,0x50,0x45,0x45,0xcb,0x49,0xce,0x55,
0x53,0xd2,0x53,0x54,0x52,0xa4,0x43,0x48,0x52,0xa4,0x4e,0x4f,0xd4,0x42,0x49,0xce,
0x4f,0xd2,0x41,0x4e,0xc4,0x3c,0xbd,0x3e,0xbd,0x3c,0xbe,0x4c,0x49,0x4e,0xc5,0x54,
0x48,0x45,0xce,0x54,0xcf,0x53,0x54,0x45,0xd0,0x44,0x45,0x46,0x20,0x46,0xce,0x43,
0x41,0xd4,0x46,0x4f,0x52,0x4d,0x41,0xd4,0x4d,0x4f,0x56,0xc5,0x45,0x52,0x41,0x53,
0xc5,0x4f,0x50,0x45,0x4e,0x20,0xa3,0x43,0x4c,0x4f,0x53,0x45,0x20,0xa3,0x4d,0x45,
0x52,0x47,0xc5,0x56,0x45,0x52,0x49,0x46,0xd9,0x42,0x45,0x45,0xd0,0x43,0x49,0x52,
0x43,0x4c,0xc5,0x49,0x4e,0xcb,0x50,0x41,0x50,0x45,0xd2,0x46,0x4c,0x41,0x53,0xc8,
0x42,0x52,0x49,0x47,0x48,0xd4,0x49,0x4e,0x56,0x45,0x52,0x53,0xc5,0x4f,0x56,0x45,
0xd2,0x4f,0x55,0xd4,0x4c,0x50,0x52,0x49,0x4e,0xd4,0x4c,0x4c,0x49,0x53,0xd4,0x53,
0x54,0x4f,0xd0,0x52,0x45,0x41,0xc4,0x44,0x41,0x54,0xc1,0x52,0x45,0x53,0x54,0x4f,
0x52,0xc5,0x4e,0x45,0xd7,0x42,0x4f,0x52,0x44,0x45,0xd2,0x43,0x4f,0x4e,0x54,0x49,
0x4e,0x55,0xc5,0x44,0x49,0xcd,0x52,0x45,0xcd,0x46,0x4f,0xd2,0x47,0x4f,0x20,0x54,
0xcf,0x47,0x4f,0x20,0x53,0x55,0xc2,0x49,0x4e,0x50,0x55,0xd4,0x4c,0x4f,0x41,0xc4,
0x4c,0x49,0x53,0xd4,0x4c,0x45,0xd4,0x50,0x41,0x55,0x53,0xc5,0x4e,0x45,0x58,0xd4,
0x50,0x4f,0x4b,0xc5,0x50,0x52,0x49,0x4e,0xd4,0x50,0x4c,0x4f,0xd4,0x52,0x55,0xce,
0x53,0x41,0x56,0xc5,0x52,0x41,0x4e,0x44,0x4f,0x4d,0x49,0x5a,0xc5,0x49,0xc6,0x43,
0x4c,0xd3,0x44,0x52,0x41,0xd7,0x43,0x4c,0x45,0x41,0xd2,0x52,0x45,0x54,0x55,0x52,
0xce,0x43,0x4f,0x50,0xd9,0x42,0x48,0x59,0x36,0x35,0x54,0x47,0x56,0x4e,0x4a,0x55,
0x37,0x34,0x52,0x46,0x43,0x4d,0x4b,0x49,0x38,0x33,0x45,0x44,0x58,0x0e,0x4c,0x4f,
0x39,0x32,0x57,0x53,0x5a,0x20,0x0d,0x50,0x30,0x31,0x51,0x41,0xe3,0xc4,0xe0,0xe4,
0xb4,0xbc,0xbd,0xbb,0xaf,0xb0,0xb1,0xc0,0xa7,0xa6,0xbe,0xad,0xb2,0xba,0xe5,0xa5,
0xc2,0xe1,0xb3,0xb9,0xc1,0xb8,0x7e,0xdc,0xda,0x5c,0xb7,0x7b,0x7d,0xd8,0xbf,0xae,
0xaa,0xab,0xdd,0xde,0xdf,0x7f,0xb5,0xd6,0x7c,0xd5,0x5d,0xdb,0xb6,0xd9,0x5b,0xd7,
0x0c,0x07,0x06,0x04,0x05,0x08,0x0a,0x0b,0x09,0x0f,0xe2,0x2a,0x3f,0xcd,0xc8,0xcc,
0xcb,0x5e,0xac,0x2d,0x2b,0x3d,0x2e,0x2c,0x3b,0x22,0xc7,0x3c,0xc3,0x3e,0xc5,0x2f,
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
};
