djspawnbrest/ESP32AY/src/players/MODPlay.h

#include <AudioGeneratorMOD.h>

AudioGeneratorMOD *mod;
static bool modOutInitialized=false;  // FIX: Prevent multiple initOut() calls

void setModSeparation(){
  if(mod) mod->SetSeparation(lfsConfig.modStereoSeparation);
}

void MOD_Cleanup(){
  if(mod) mod->stop();
  memset(modEQchn,0,sizeof(modEQchn));
  memset(bufEQ,0,sizeof(bufEQ));
  memset(&music_data,0,sizeof(music_data));
  memset(&AYInfo,0,sizeof(AYInfo));
  modFile->close();
  delete mod;
  delete modFile;
  mod=nullptr;
  modFile=nullptr;
  out->stop();
  vTaskDelay(pdMS_TO_TICKS(10));
  skipMod=false;
  modOutInitialized=false;  // FIX: Reset flag for next track
}

void MOD_GetInfo(const char *filename){
  modFile=new AudioFileSourceSDFAT(sdCardSemaphore);
  mod=new AudioGeneratorMOD();
  #if !defined(CONFIG_IDF_TARGET_ESP32S3)&&!defined(BOARD_HAS_PSRAM)
  mod->SetBufferSize(1024*6);
  #endif
  mod->SetStereoSeparation(lfsConfig.modStereoSeparation);
  modFile->open(filename);
  bool status=mod->initializeFile(modFile);
  if(!status){
    // FIX FOR MEMORY LEAK - delete objects if initialization failed
    AYInfo.Length=1;
    skipMod=true;
    if(mod){
      delete mod;
      mod=nullptr;
    }
    if(modFile){
      modFile->close();
      delete modFile;
      modFile=nullptr;
    }
    return;
  }
  mod->initEQBuffers(bufEQ,modEQchn);
  modChannels=mod->getNumberOfChannels();
  modChannelsEQ=(modChannels>8)?8:modChannels;
  #if !defined(CONFIG_IDF_TARGET_ESP32S3)&&!defined(BOARD_HAS_PSRAM)
  if(modChannels<2||modChannels>16){
    AYInfo.Length=1;
    skipMod=true;
    // FIX FOR MEMORY LEAK - delete objects if channel check failed
    if(mod){
      delete mod;
      mod=nullptr;
    }
    if(modFile){
      modFile->close();
      delete modFile;
      modFile=nullptr;
    }
    return;
  }
  #else
  if(modChannels<2||modChannels>32){
    AYInfo.Length=1;
    skipMod=true;
    // FIX FOR MEMORY LEAK - delete objects if channel check failed
    if(mod){
      delete mod;
      mod=nullptr;
    }
    if(modFile){
      modFile->close();
      delete modFile;
      modFile=nullptr;
    }
    return;
  }
  #endif
  AYInfo.Length=mod->getPlaybackTime();
  mod->getTitle(AYInfo.Name,sizeof(AYInfo.Name));
  mod->getDescription(AYInfo.Author,sizeof(AYInfo.Author));
  mod->initTrackFrame(&PlayerCTRL.trackFrame);
}

void MOD_Loop() {
  if(skipMod){PlayerCTRL.isFinish=true;return;}
  if(mod&&mod->isRunning()&&PlayerCTRL.isPlay){
    if(!mod->loop()){
      mod->stop();
      PlayerCTRL.isFinish=true;
    }
  }
}

void MOD_Play(){
  if(mod&&!mod->isRunning()){
    // FIX: Only call initOut() once per track, not every frame
    if(!modOutInitialized){
      initOut();
      modOutInitialized=true;
    }
    mod->begin(modFile,out);
  }
  MOD_Loop();
}
