djspawnbrest/ESP32AY/src/players/S3MPlay.h

#include <AudioGeneratorS3M.h>

AudioGeneratorS3M *s3m;
static bool s3mOutInitialized=false;  // FIX: Prevent multiple initOut() calls

void setS3mSeparation(){
  if(s3m) s3m->SetSeparation(lfsConfig.modStereoSeparation);
}

void S3M_Cleanup(){
  if(s3m) s3m->stop();
  memset(modEQchn,0,sizeof(modEQchn));
  memset(bufEQ,0,sizeof(bufEQ));
  memset(&music_data,0,sizeof(music_data));
  memset(&AYInfo,0,sizeof(AYInfo));
  modFile->close();
  delete s3m;
  delete modFile;
  s3m=nullptr;
  modFile=nullptr;
  out->stop();
  vTaskDelay(pdMS_TO_TICKS(10));
  skipMod=false;
  s3mOutInitialized=false;  // FIX: Reset flag for next track
}

void S3M_GetInfo(const char *filename){
  modFile=new AudioFileSourceSDFAT(sdCardSemaphore);
  s3m=new AudioGeneratorS3M();
  s3m->SetStereoSeparation(lfsConfig.modStereoSeparation);
  modFile->open(filename);
  bool status=s3m->initializeFile(modFile);
  if(!status){
    // FIX FOR MEMORY LEAK - delete objects if initialization failed
    AYInfo.Length=1;
    skipMod=true;
    if(s3m){
      delete s3m;
      s3m=nullptr;
    }
    if(modFile){
      modFile->close();
      delete modFile;
      modFile=nullptr;
    }
    return;
  }
  s3m->initEQBuffers(bufEQ,modEQchn);
  modChannels=s3m->getNumberOfChannels();
  modChannelsEQ=(modChannels>8)?8:modChannels;
  #if !defined(CONFIG_IDF_TARGET_ESP32S3)&&!defined(BOARD_HAS_PSRAM)
  if(modChannels<2||modChannels>16){
    AYInfo.Length=1;
    skipMod=true;
    // FIX FOR MEMORY LEAK - delete objects if channel check failed
    if(s3m){
      delete s3m;
      s3m=nullptr;
    }
    if(modFile){
      modFile->close();
      delete modFile;
      modFile=nullptr;
    }
    return;
  }
  #else
  if(modChannels<2||modChannels>32){
    AYInfo.Length=1;
    skipMod=true;
    // FIX FOR MEMORY LEAK - delete objects if channel check failed
    if(s3m){
      delete s3m;
      s3m=nullptr;
    }
    if(modFile){
      modFile->close();
      delete modFile;
      modFile=nullptr;
    }
    return;
  }
  #endif
  AYInfo.Length=s3m->getPlaybackTime();
  s3m->getTitle(AYInfo.Name,sizeof(AYInfo.Name));
  s3m->getDescription(AYInfo.Author,sizeof(AYInfo.Author));
  s3m->initTrackFrame(&PlayerCTRL.trackFrame);
  #if !defined(CONFIG_IDF_TARGET_ESP32S3)&&!defined(BOARD_HAS_PSRAM)
	s3m->SetSampleRate((modChannels>14)?32000:44100);
  #endif
}
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
